bitfieldlabs/afterglow/afterglow_whitestar_pcb_v21/afterglow_whitestar_pcb_20_render.jpg

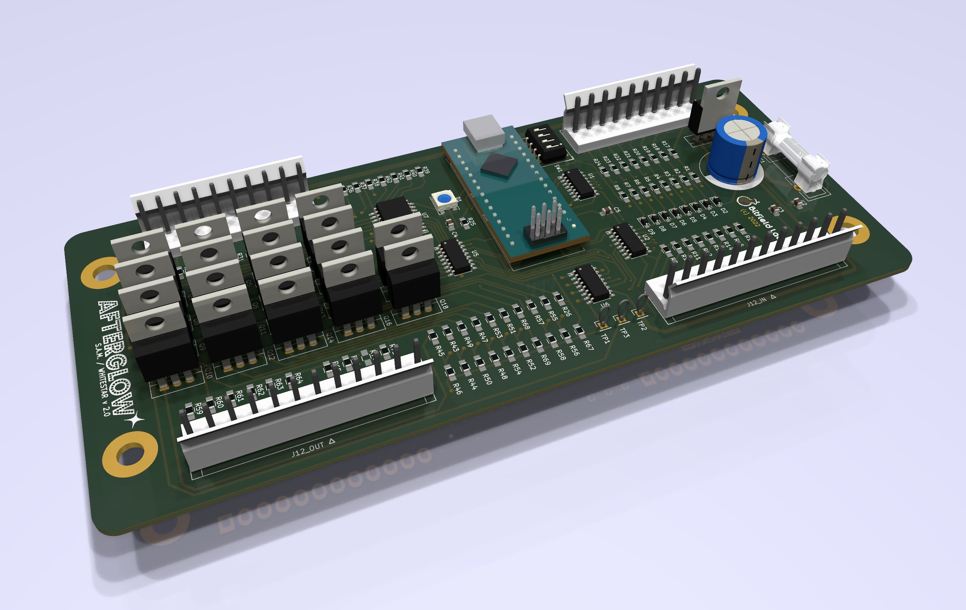
afterglow_whitestar_pcb_v21/afterglow_whitestar_pcb_20_render.jpg
