bitfieldlabs/afterglow/artwork/afterglow_config_v01.png

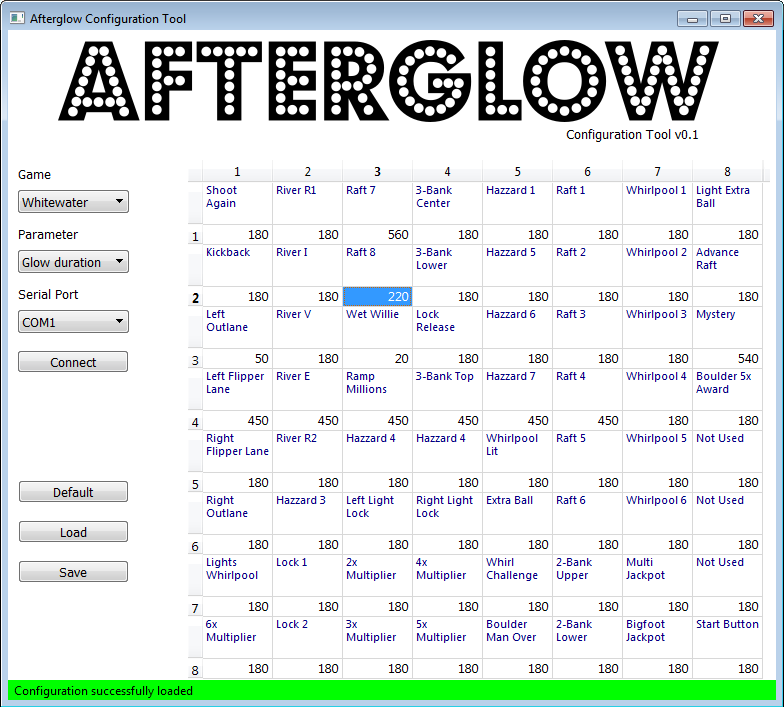
artwork/afterglow_config_v01.png
