bitfieldlabs/afterglow/docu/images/afterglow_config_0.7.png

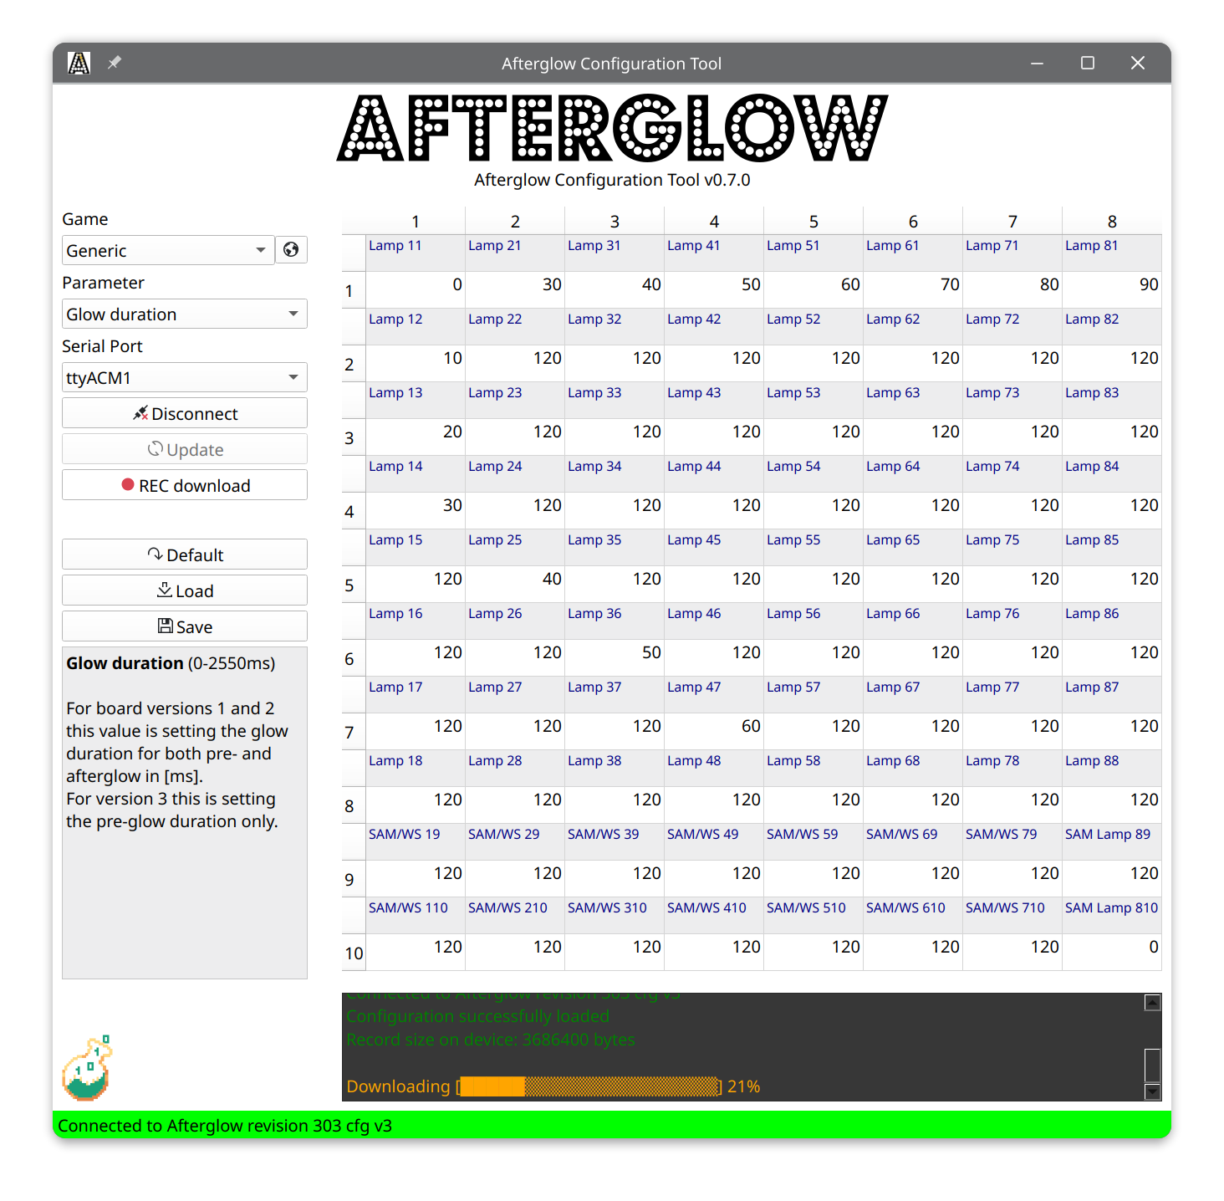
docu/images/afterglow_config_0.7.png
