bitfieldlabs/afterglow/docu/images/ag_30_dip.jpg

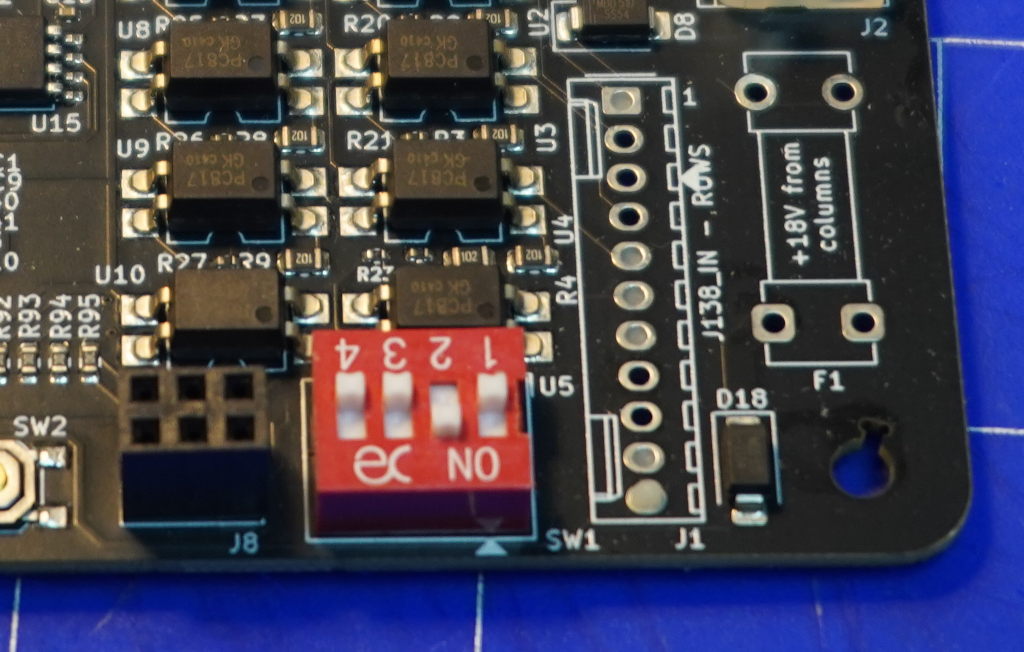
docu/images/ag_30_dip.jpg
