bitfieldlabs/afterglow/docu/images/ag_30_hats.jpg

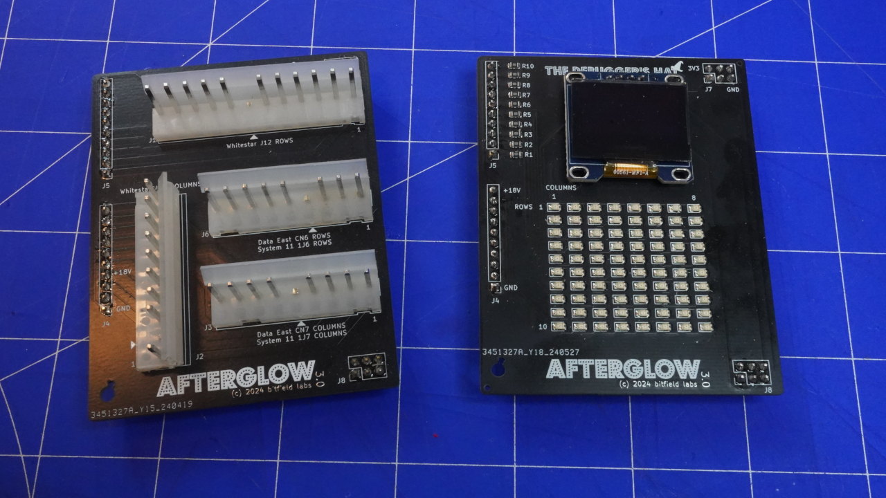
docu/images/ag_30_hats.jpg
