bitfieldlabs/afterglow/docu/images/ag_30g.jpg

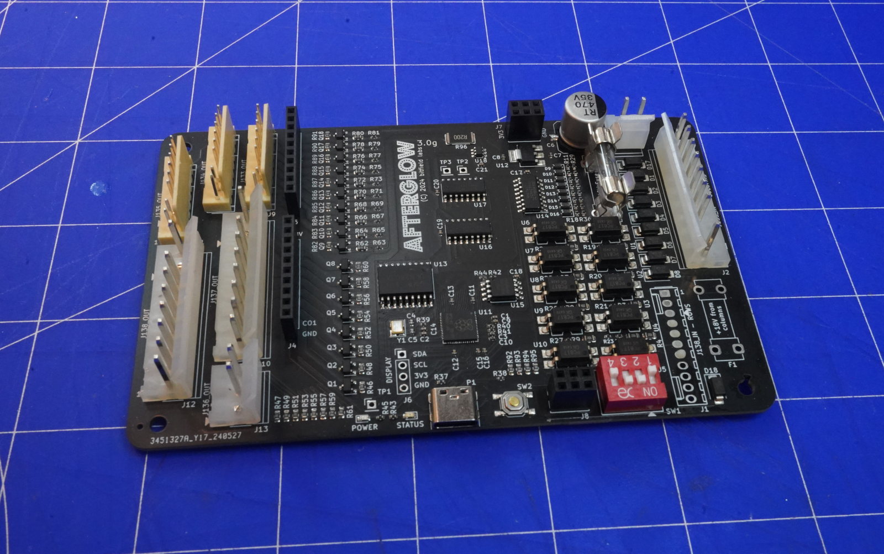
docu/images/ag_30g.jpg
