bitfieldlabs/afterglow/docu/images/ag_v13_mounting.jpg

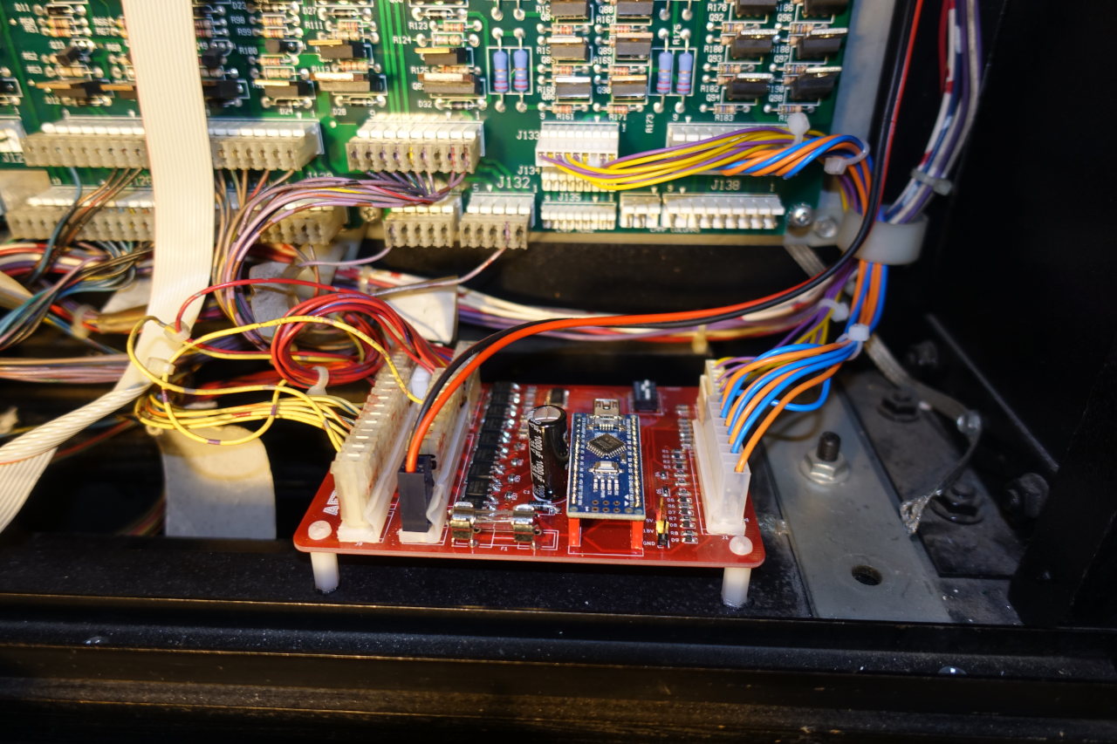
docu/images/ag_v13_mounting.jpg
