bitfieldlabs/afterglow/docu/images/ag_v13_mounting_2.jpg

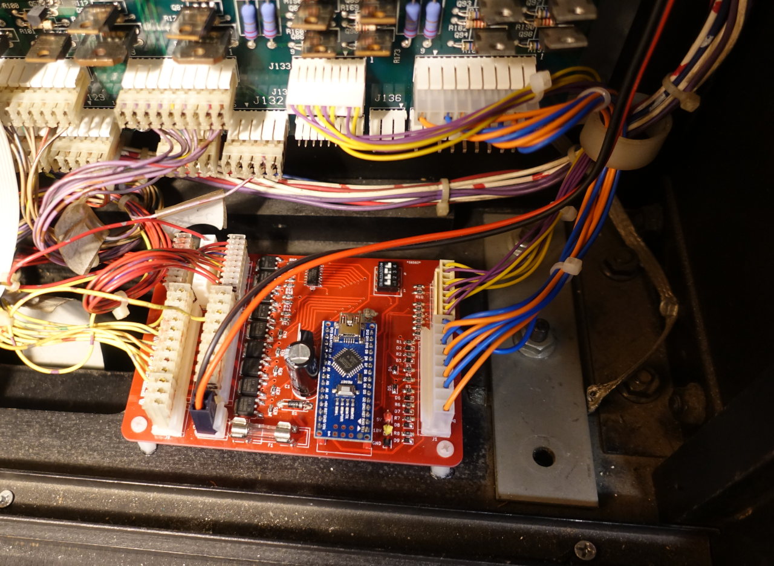
docu/images/ag_v13_mounting_2.jpg
