bitfieldlabs/afterglow/docu/images/ag_v13_mounting_3.jpg

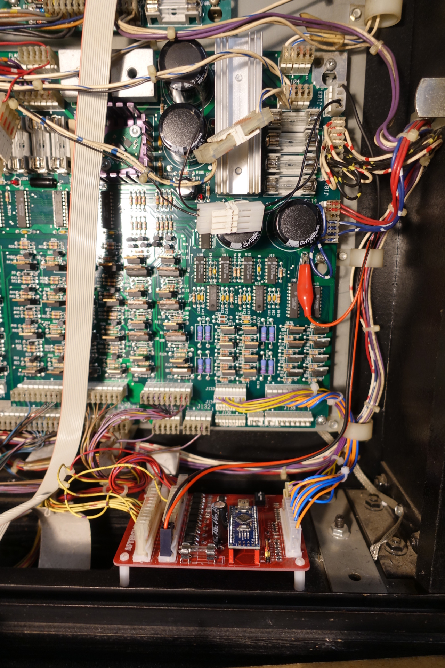
docu/images/ag_v13_mounting_3.jpg
