bitfieldlabs/afterglow/docu/images/ag_whitestar_mounting.jpg

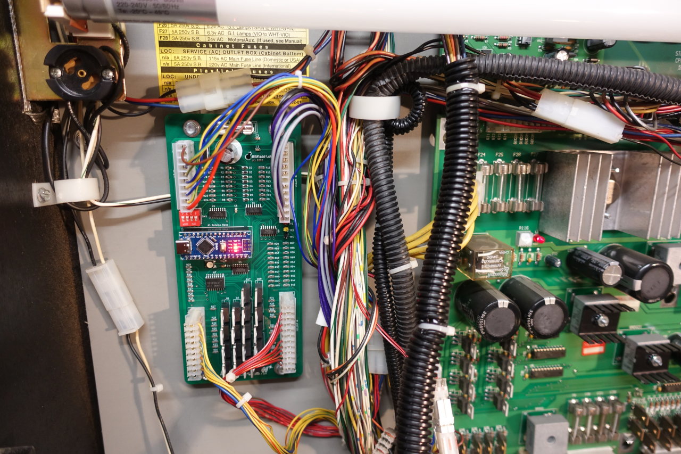
docu/images/ag_whitestar_mounting.jpg
