bitfieldlabs/afterglow/docu/images/china_led.jpg

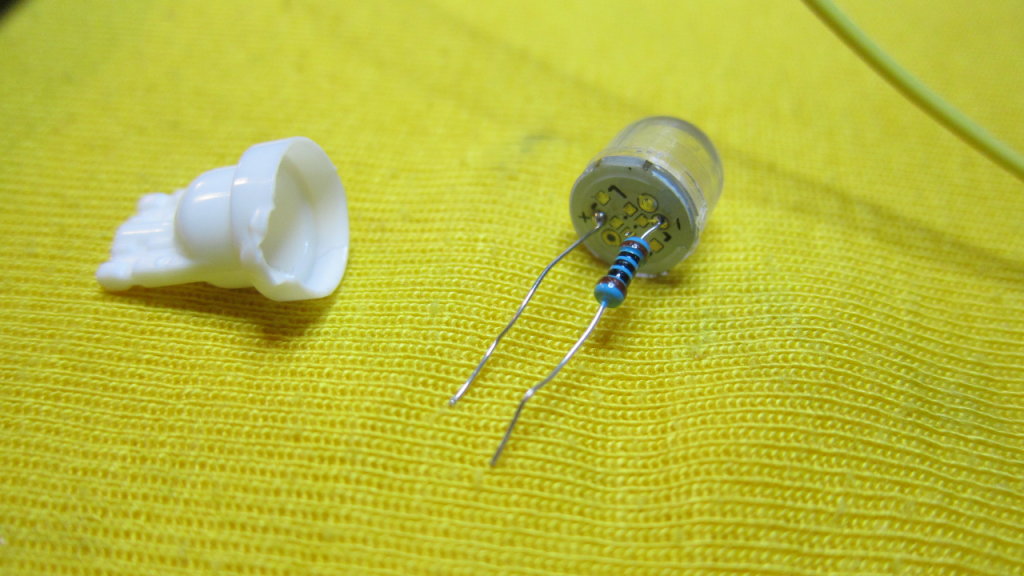
docu/images/china_led.jpg
