bitfieldlabs/afterglow/docu/images/config_switch.jpg

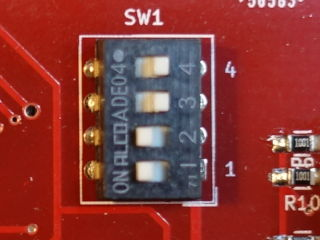
docu/images/config_switch.jpg
