bitfieldlabs/afterglow/docu/images/pcb_v10_inc.jpg

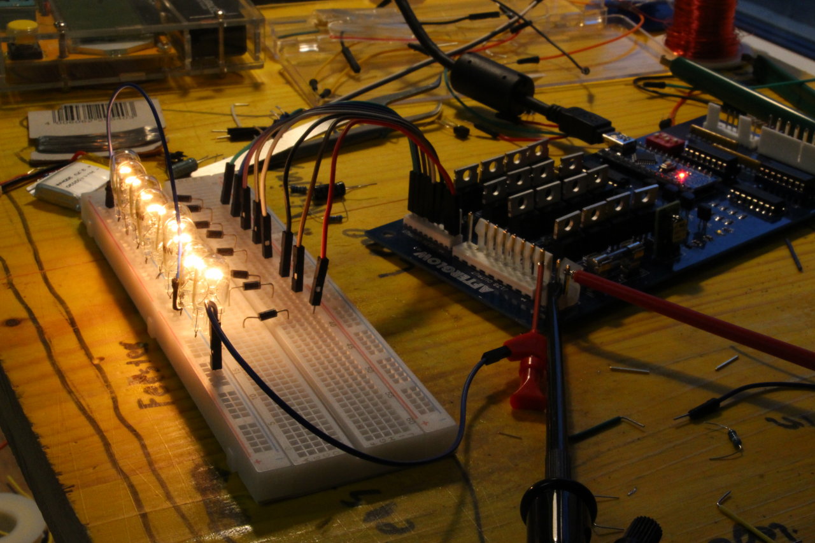
docu/images/pcb_v10_inc.jpg
