bitfieldlabs/afterglow/docu/images/pcb_v11_poulated.jpg

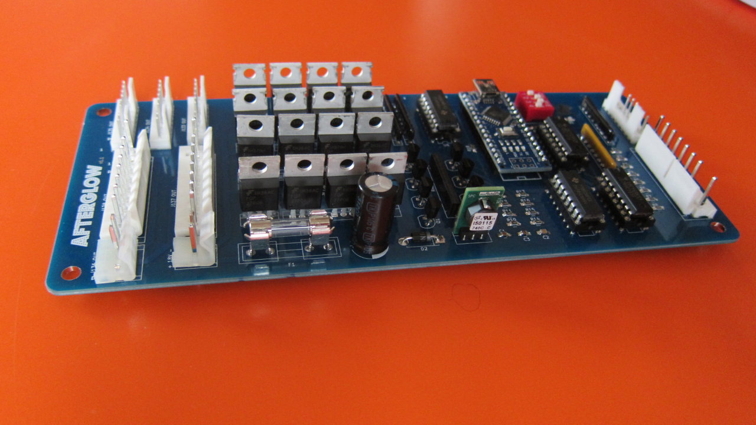
docu/images/pcb_v11_poulated.jpg
