bitfieldlabs/afterglow/docu/images/pcb_v13_populated.jpg

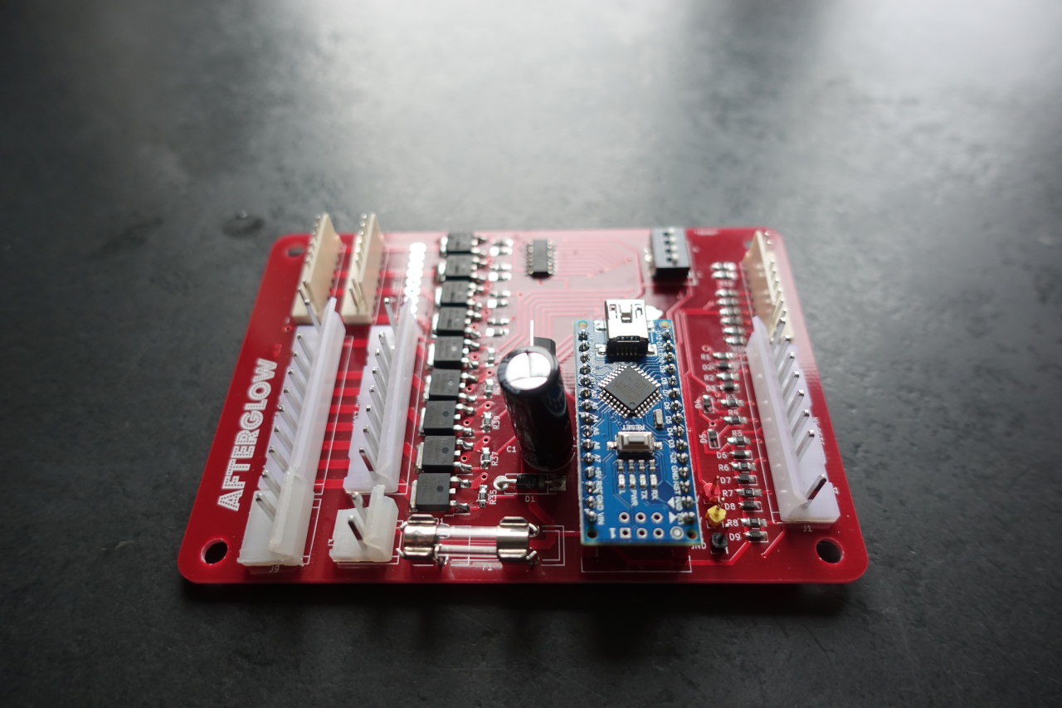
docu/images/pcb_v13_populated.jpg
