bitfieldlabs/afterglow/docu/images/pcb_v14_populated.jpg

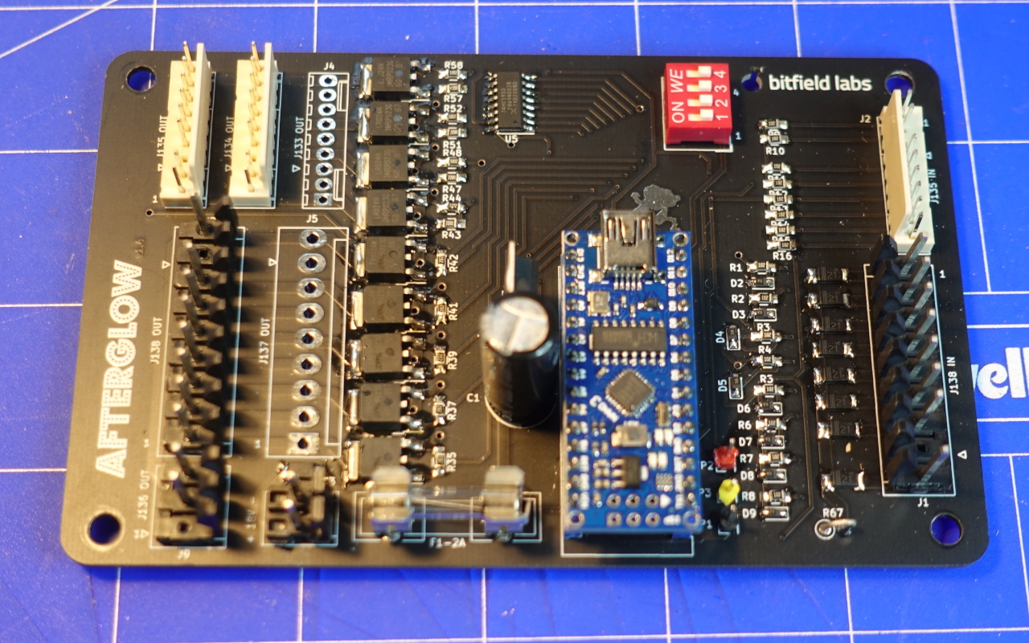
docu/images/pcb_v14_populated.jpg
