bitfieldlabs/afterglow/docu/images/pcb_v15_populated.jpg

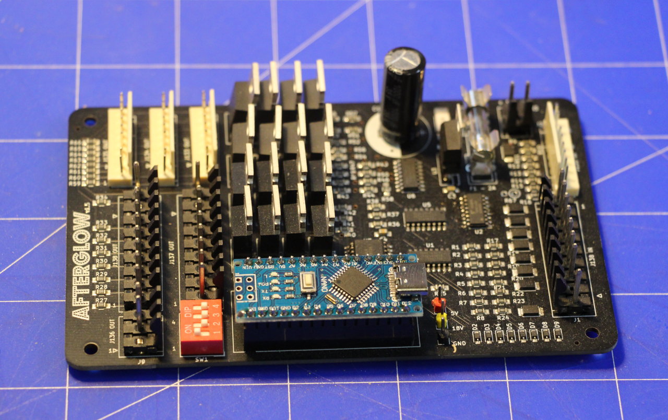
docu/images/pcb_v15_populated.jpg
