bitfieldlabs/afterglow/docu/images/pcb_v30_render.jpg

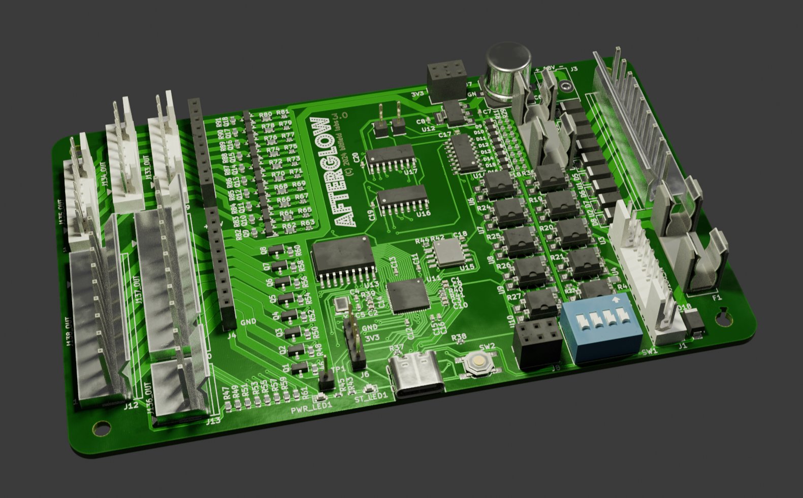
docu/images/pcb_v30_render.jpg
