bitfieldlabs/afterglow/scopes/AG/col1_col2_attract_mode.png

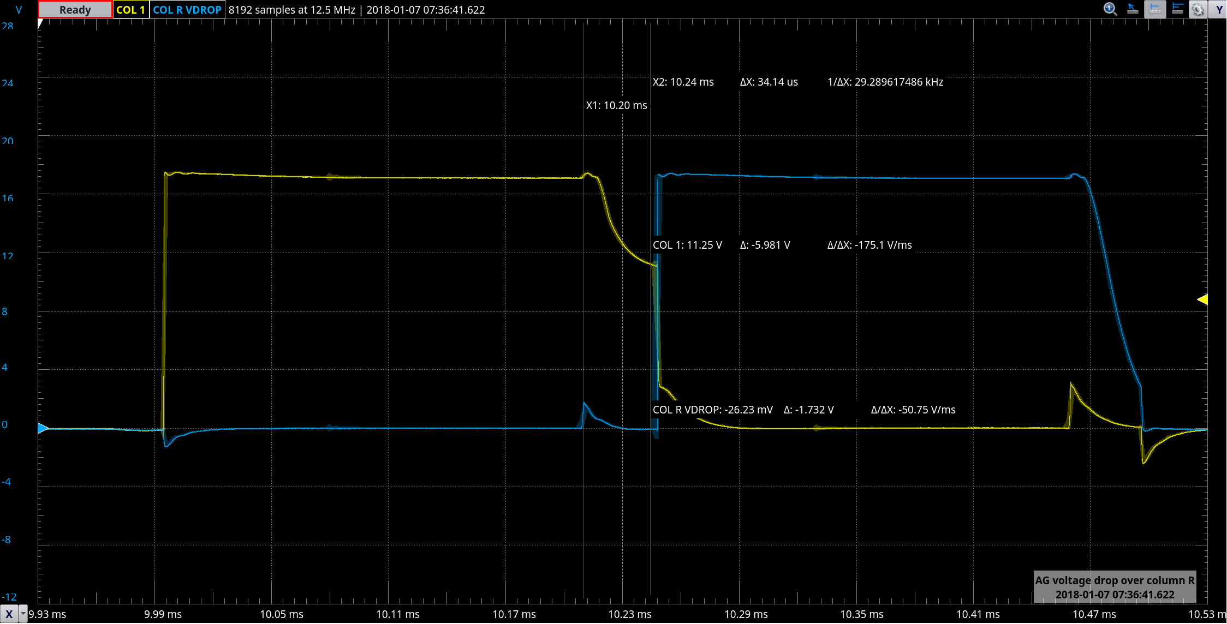
scopes/AG/col1_col2_attract_mode.png
