bitfieldlabs/afterglow/scopes/AG/vdrop_over_volumn_R.png

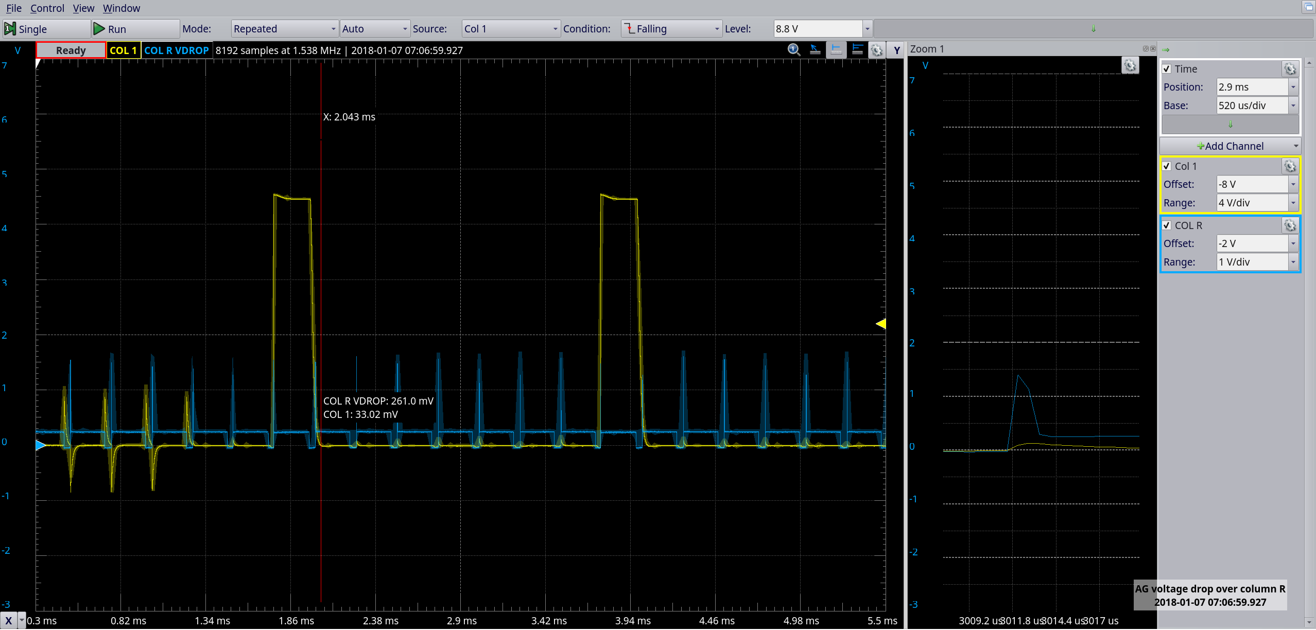
scopes/AG/vdrop_over_volumn_R.png
