bitfieldlabs/afterglow/scopes/AG/vdrop_over_volumn_R_col1_on_zoom.png

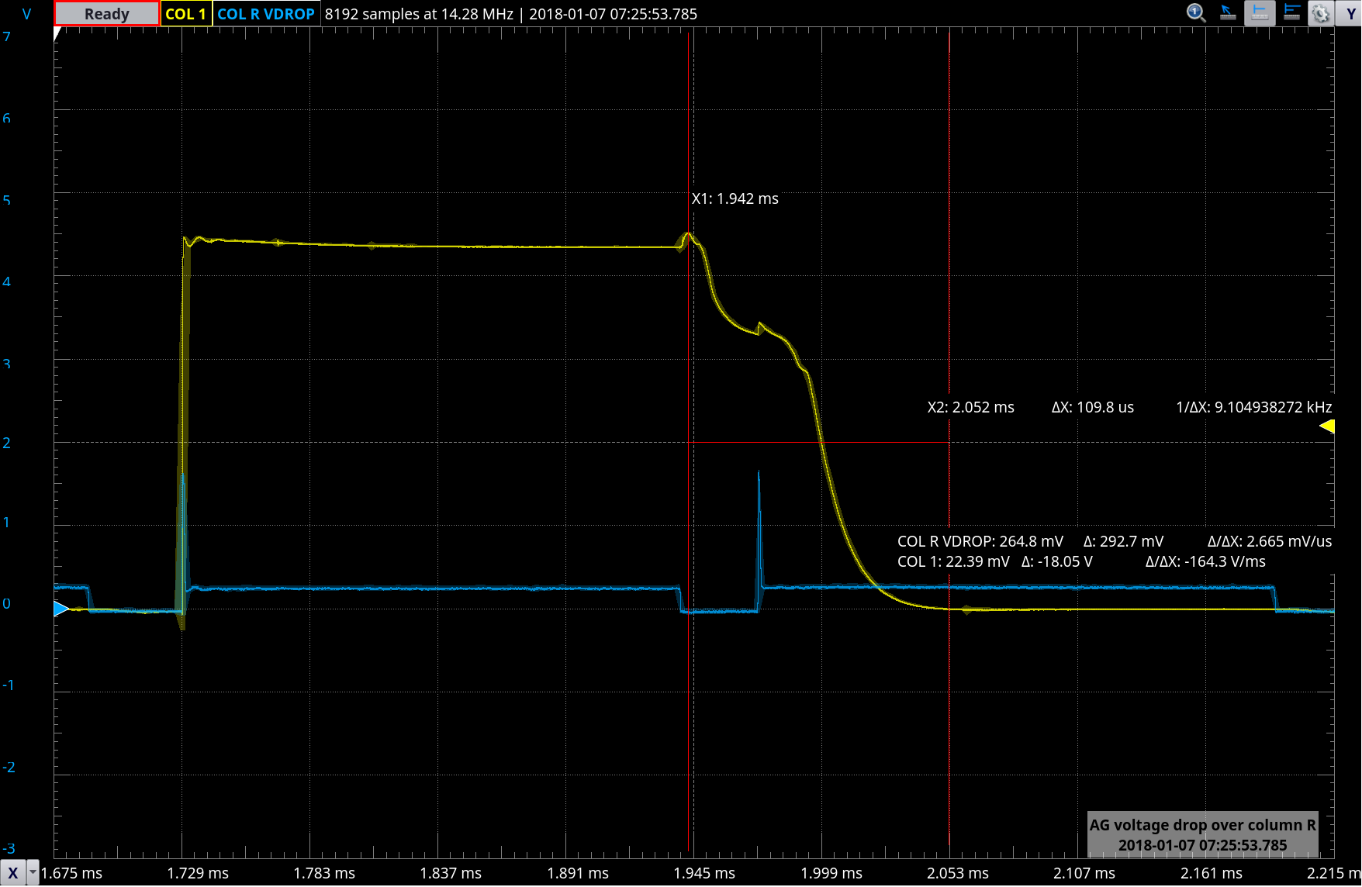
scopes/AG/vdrop_over_volumn_R_col1_on_zoom.png
