bitfieldlabs/afterglow/scopes/AG/vdrop_over_volumn_R_lamps_off.png

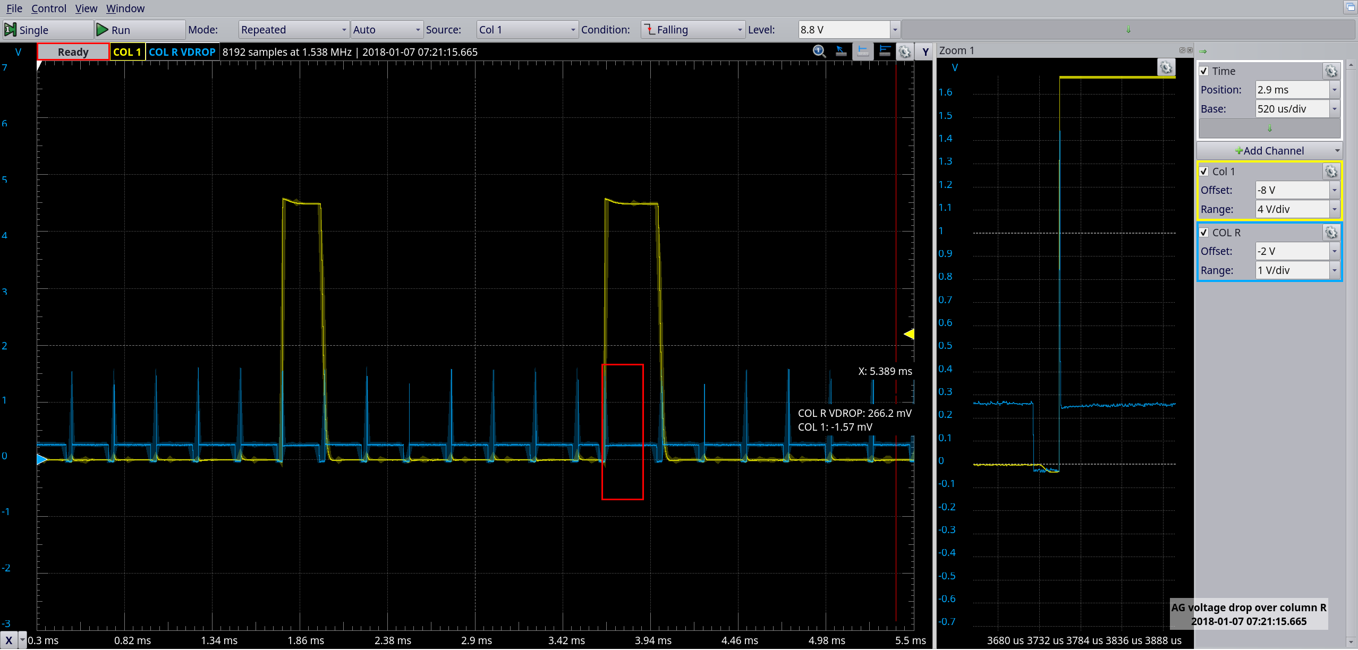
scopes/AG/vdrop_over_volumn_R_lamps_off.png
