bitfieldlabs/afterglow/scopes/AG/vdrop_over_volumn_R_lamps_off_2_annotated.png

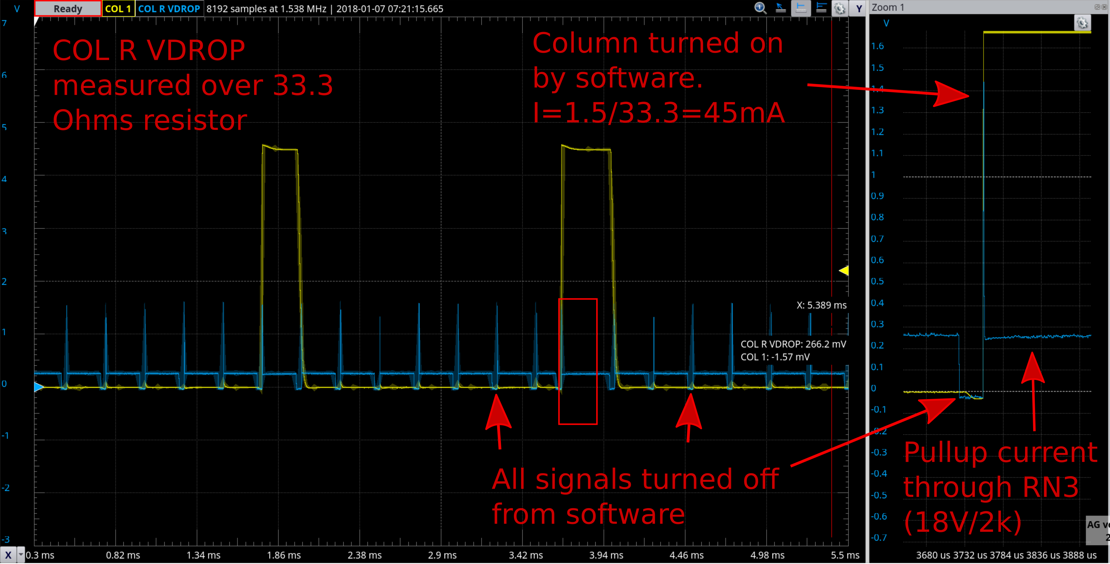
scopes/AG/vdrop_over_volumn_R_lamps_off_2_annotated.png
