bitfieldlabs/afterglow/scopes/AG/vdrop_over_volumn_R_lamps_on.png

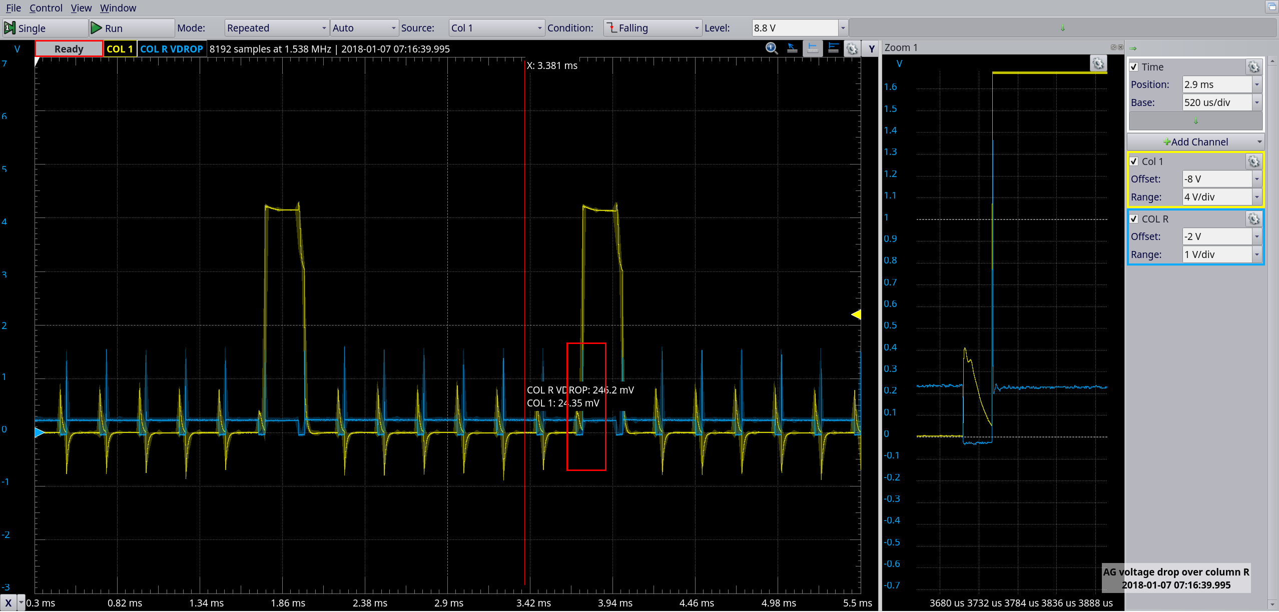
scopes/AG/vdrop_over_volumn_R_lamps_on.png
