bitfieldlabs/afterglow/scopes/AG/wh20_col1_comparison.png

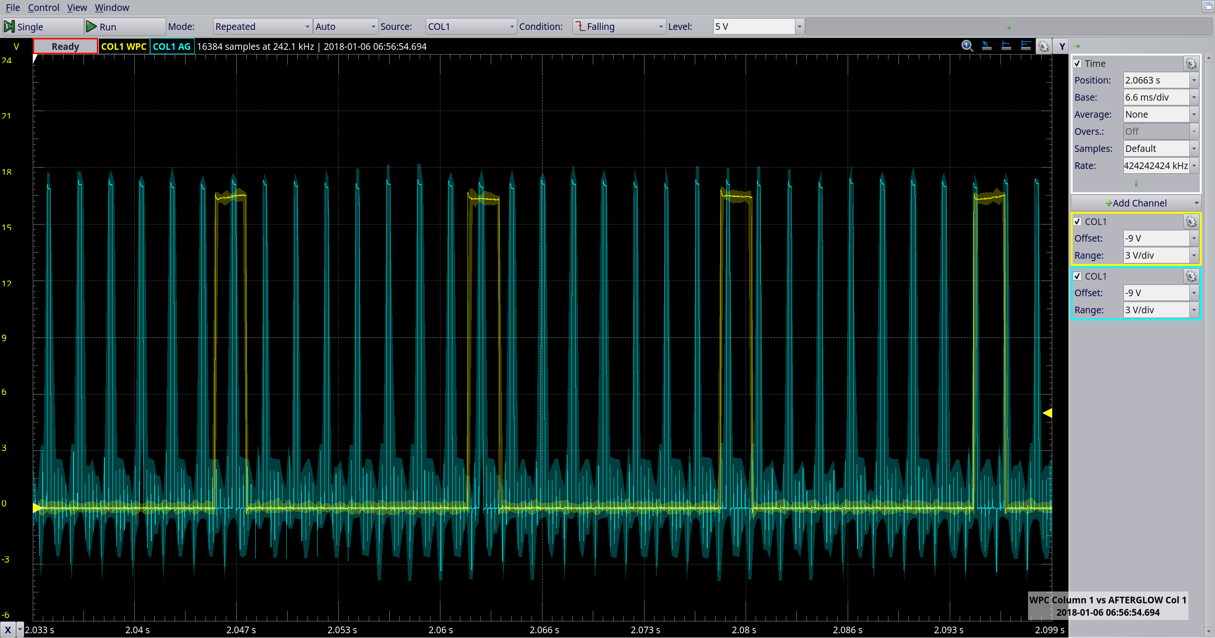
scopes/AG/wh20_col1_comparison.png
