bitfieldlabs/afterglow/scopes/AG/wh20_col1_noise.png

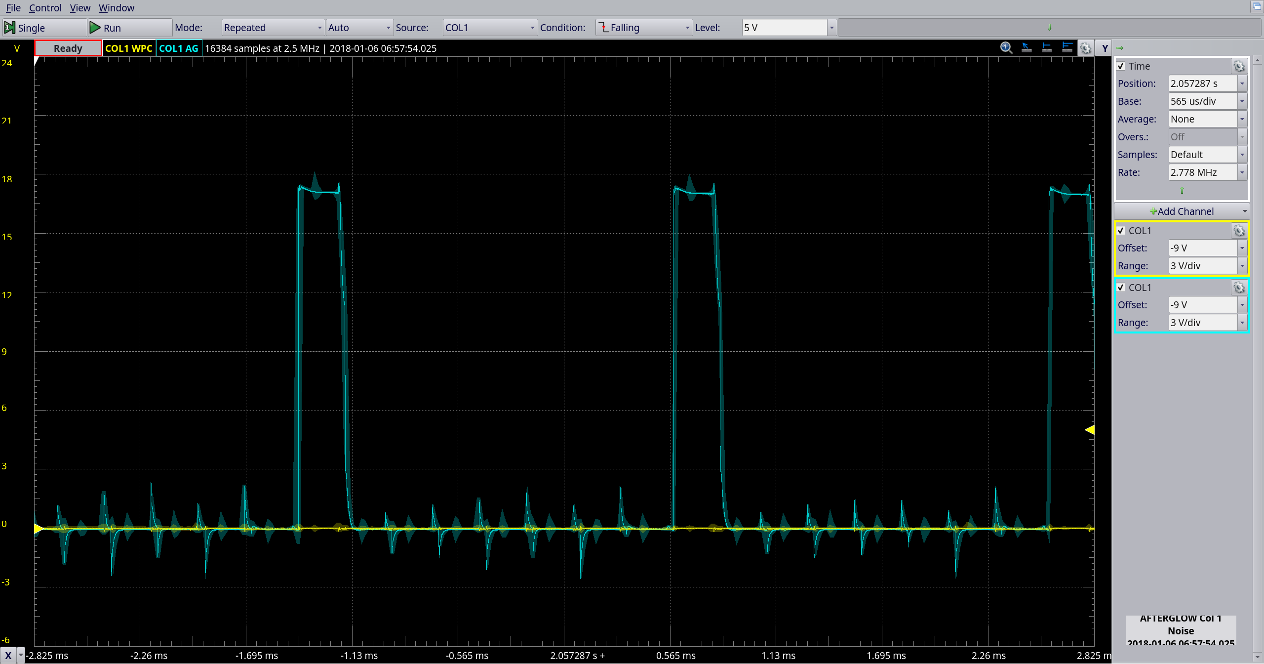
scopes/AG/wh20_col1_noise.png
