bitfieldlabs/afterglow/scopes/AG_SMD/col1_col2_lamps_connected.png

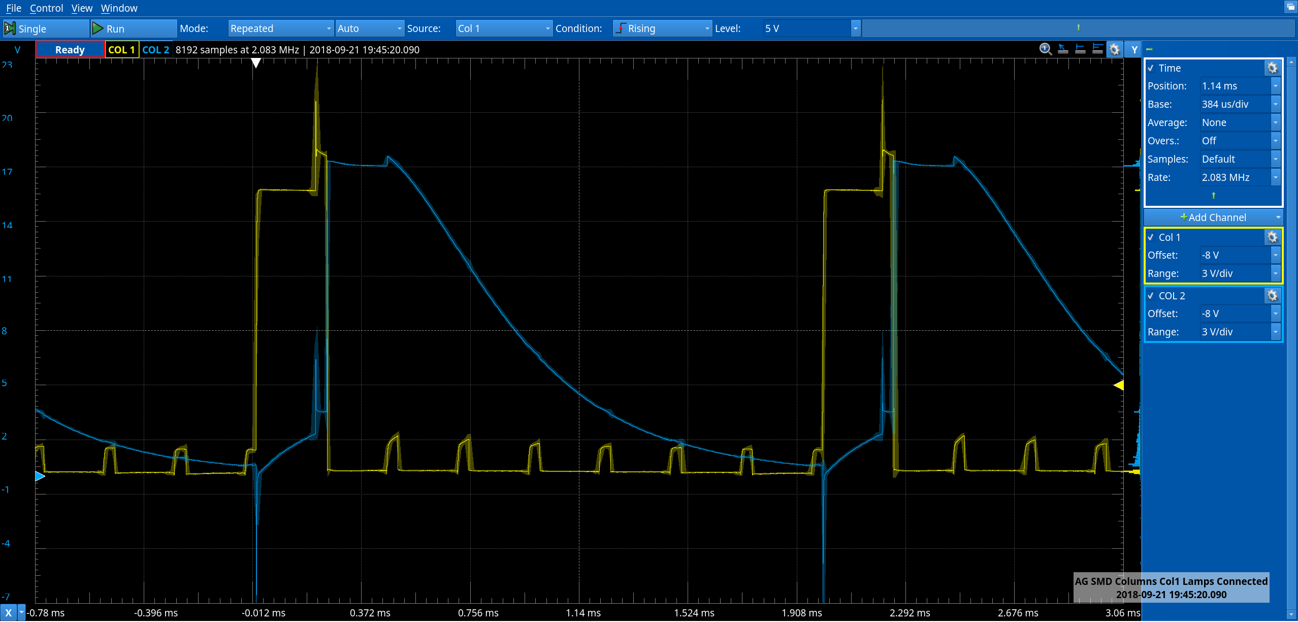
scopes/AG_SMD/col1_col2_lamps_connected.png
