bitfieldlabs/afterglow/scopes/AG_SMD/col1_col2_no_lamps_connected.png

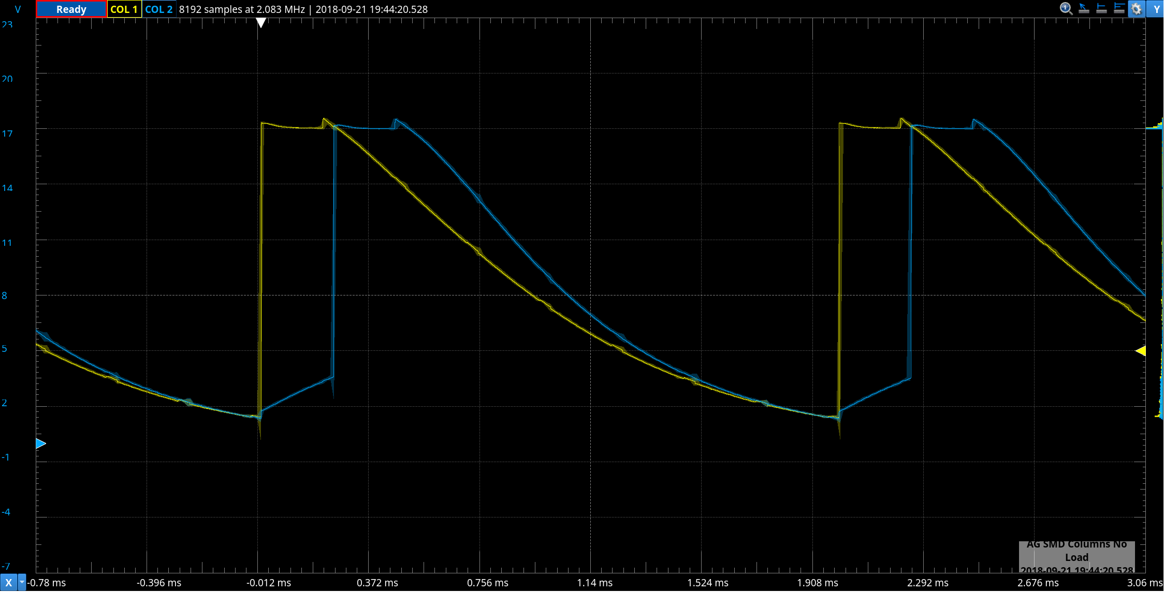
scopes/AG_SMD/col1_col2_no_lamps_connected.png
