bitfieldlabs/afterglow/scopes/AG_SMD/col1_row1_lamp_on.png

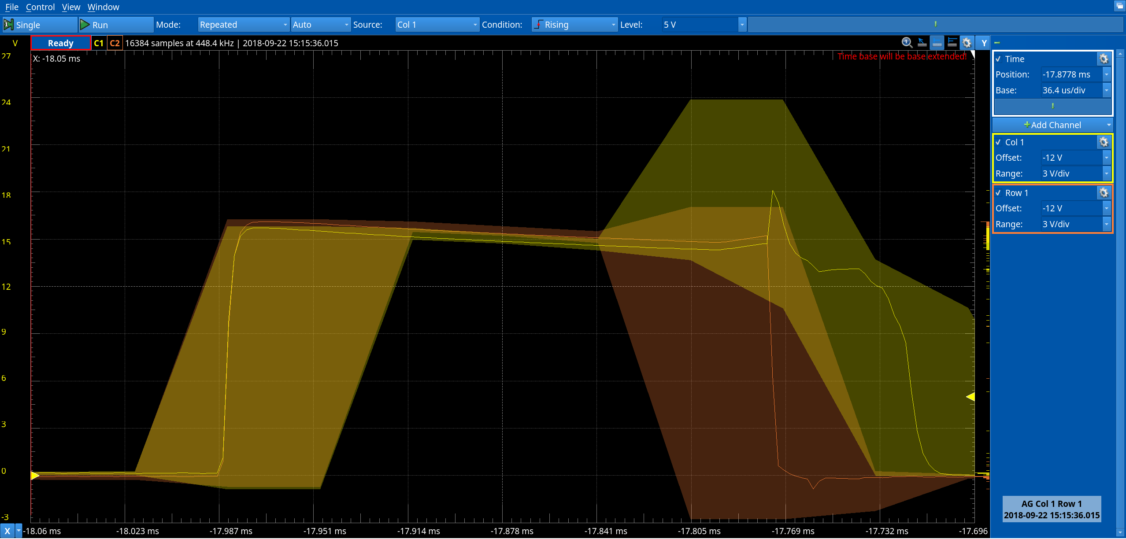
scopes/AG_SMD/col1_row1_lamp_on.png
