bitfieldlabs/afterglow/scopes/AG_SMD/col1_row1_vdrop_r27.png

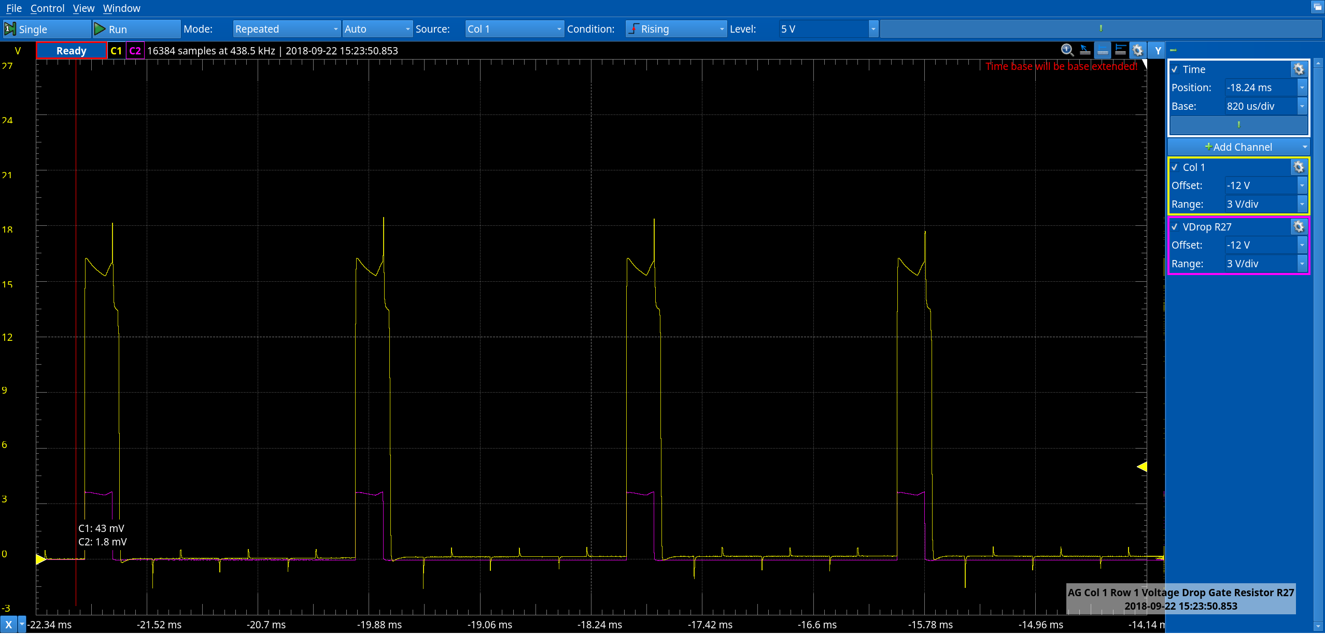
scopes/AG_SMD/col1_row1_vdrop_r27.png
