bitfieldlabs/afterglow/scopes/AG_SMD/creature_voltage_stop.png

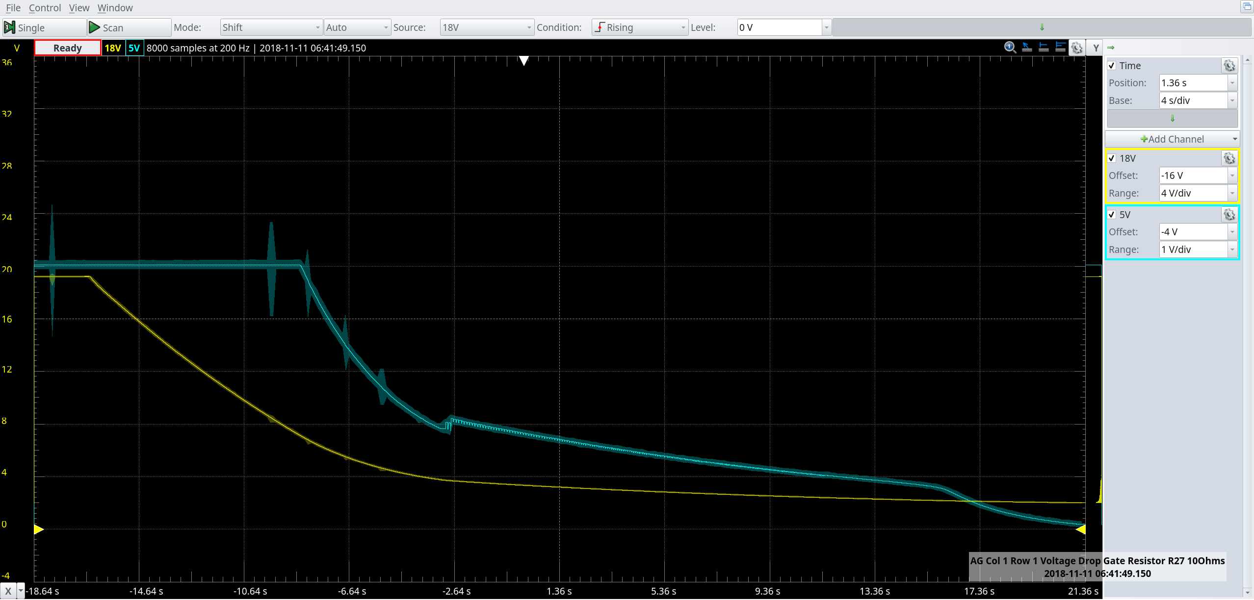
scopes/AG_SMD/creature_voltage_stop.png
