bitfieldlabs/afterglow/scopes/data_east_columns.png

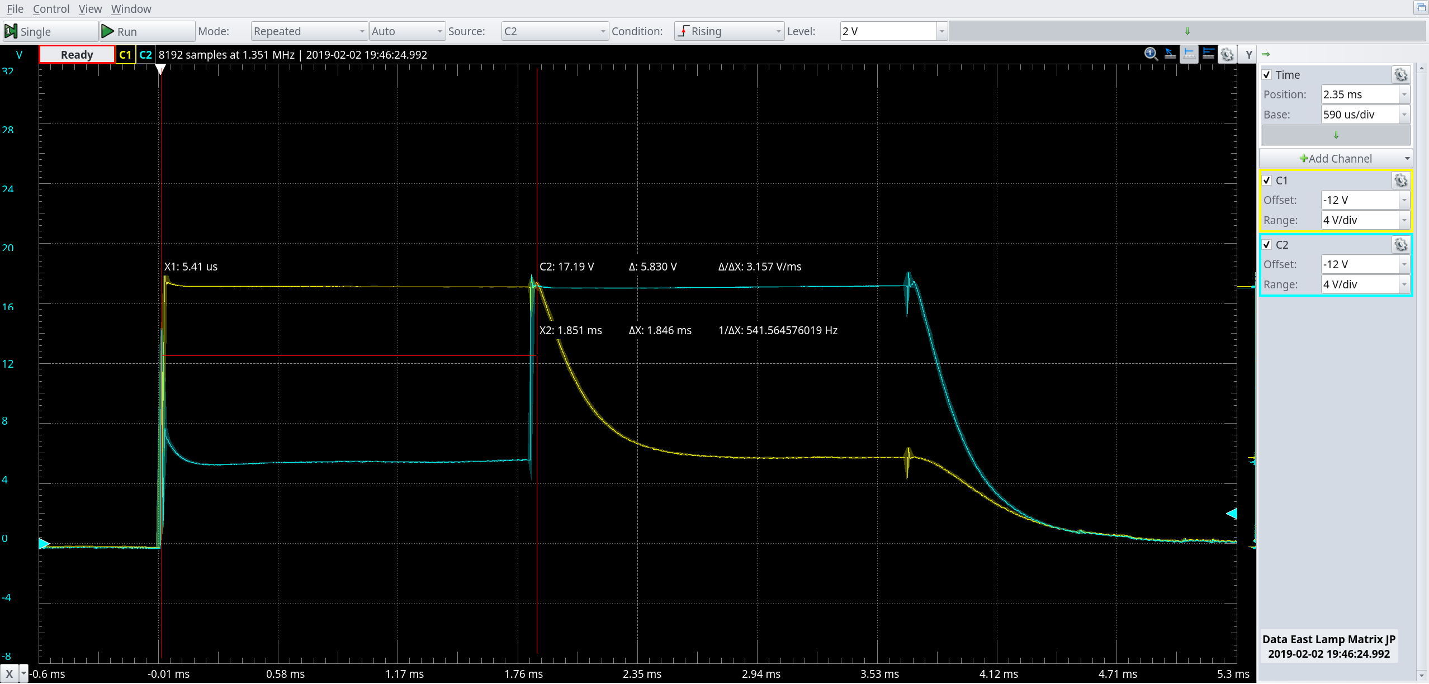
scopes/data_east_columns.png
