bitfieldlabs/afterglow/scopes/data_east_columns_2.png

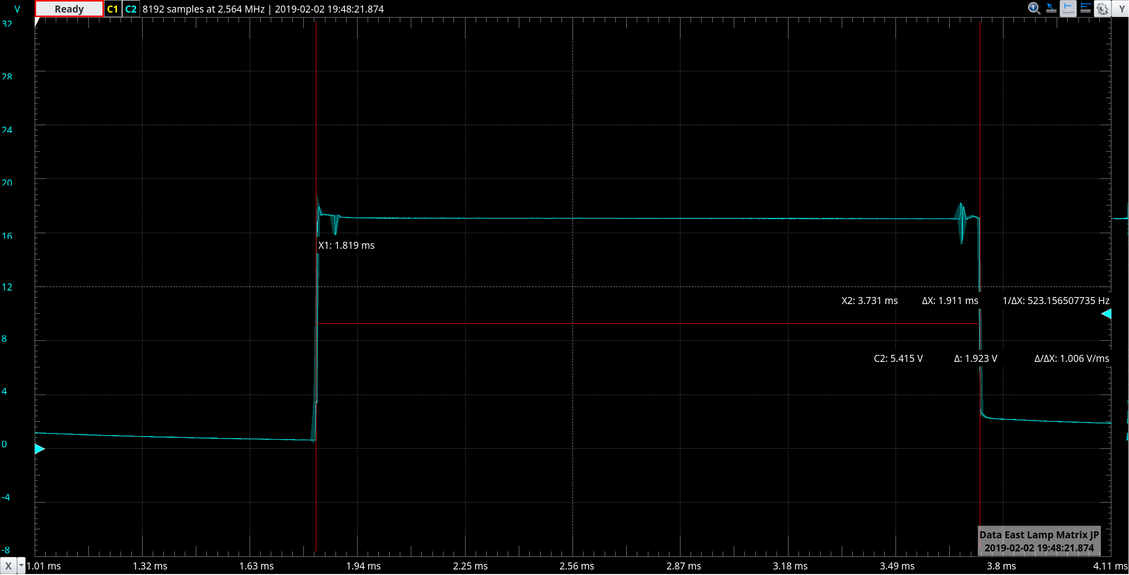
scopes/data_east_columns_2.png
