bitfieldlabs/afterglow/scopes/data_east_columns_3.png

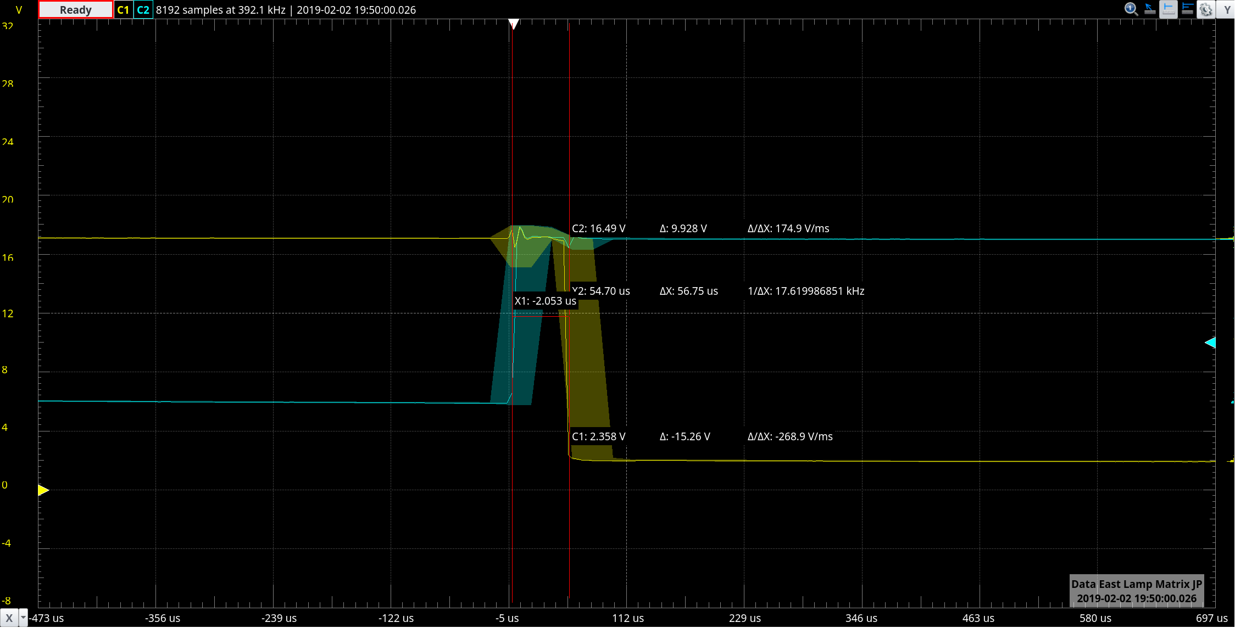
scopes/data_east_columns_3.png
