bitfieldlabs/afterglow/scopes/data_east_columns_4.png

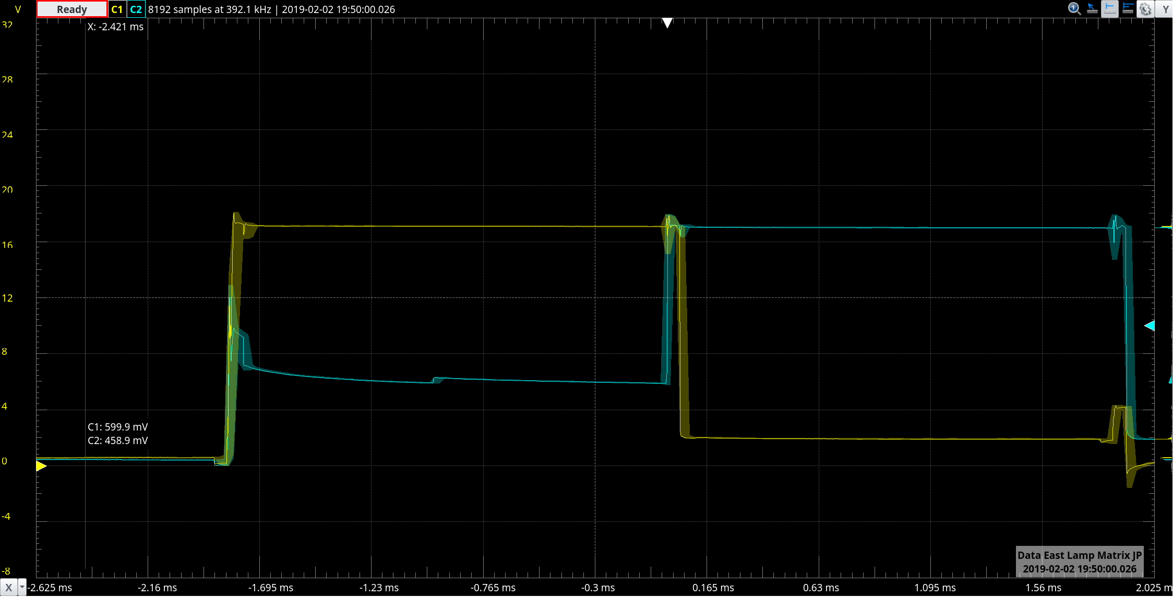
scopes/data_east_columns_4.png
