bitfieldlabs/afterglow/scopes/data_east_columns_5.png

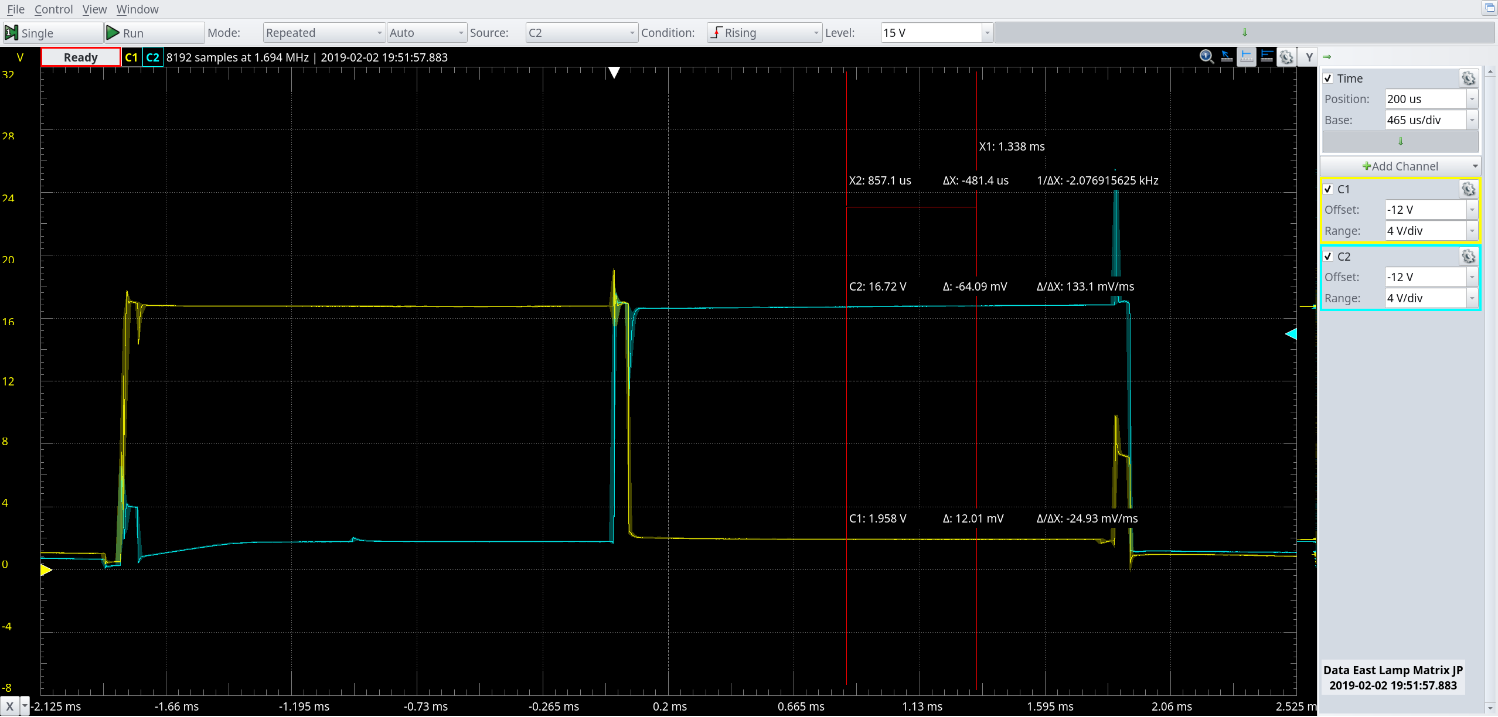
scopes/data_east_columns_5.png
