bitfieldlabs/afterglow/scopes/data_east_columns_6.png

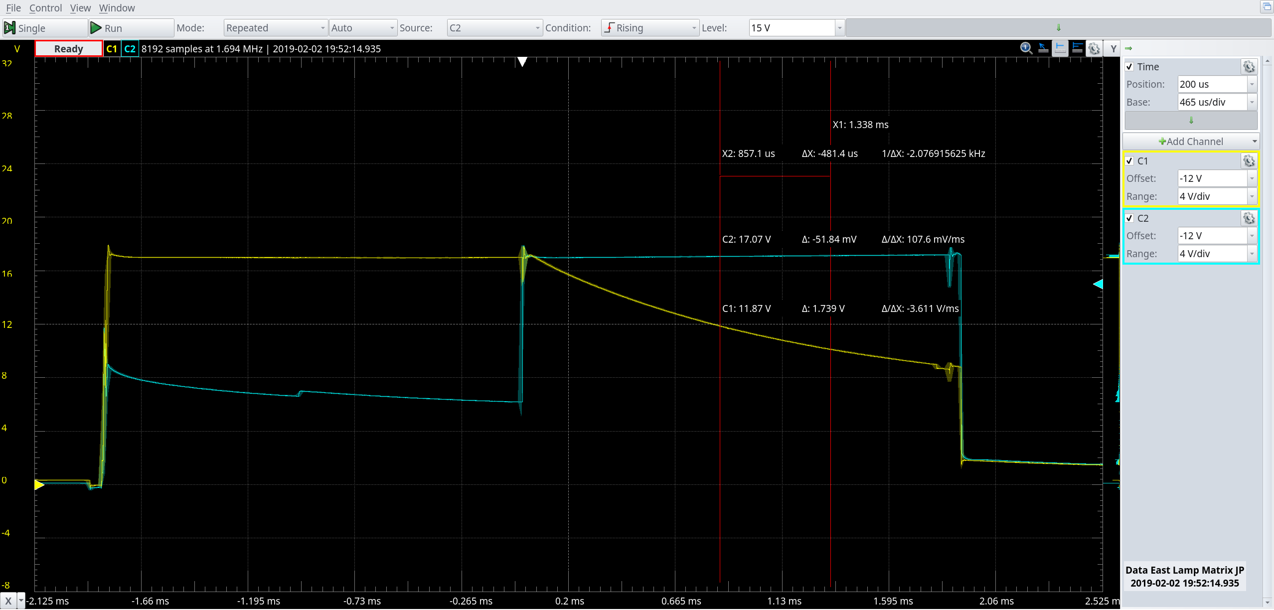
scopes/data_east_columns_6.png
