bitfieldlabs/afterglow/scopes/system_11_ww_col1_col2_2.png

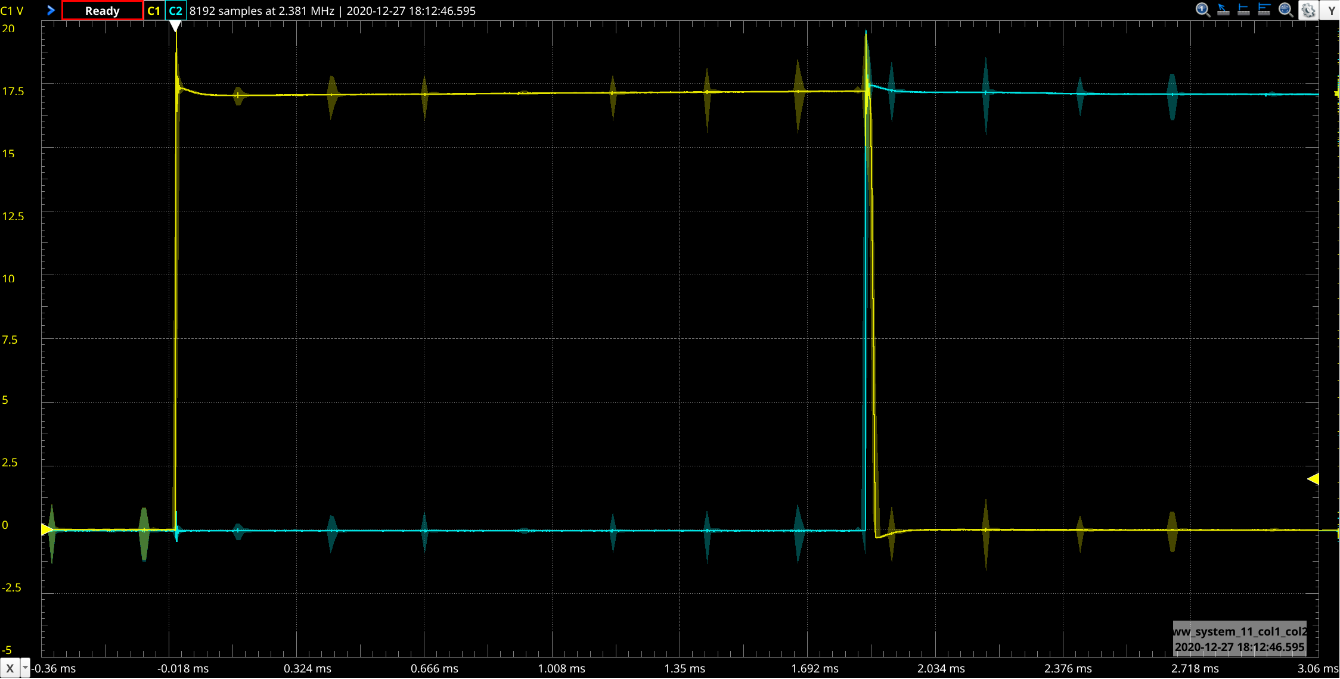
scopes/system_11_ww_col1_col2_2.png
