bitfieldlabs/afterglow/scopes/system_11_ww_col1_col2_R89_R88.png

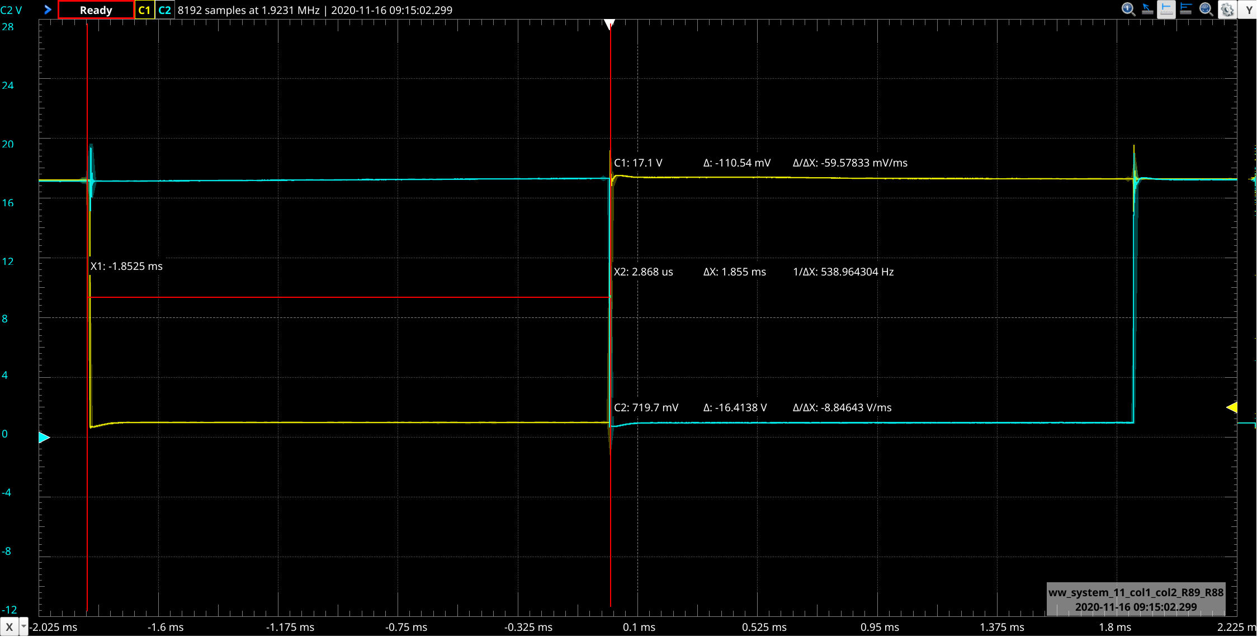
scopes/system_11_ww_col1_col2_R89_R88.png
