bitfieldlabs/afterglow/scopes/system_11_ww_col1_R89.png

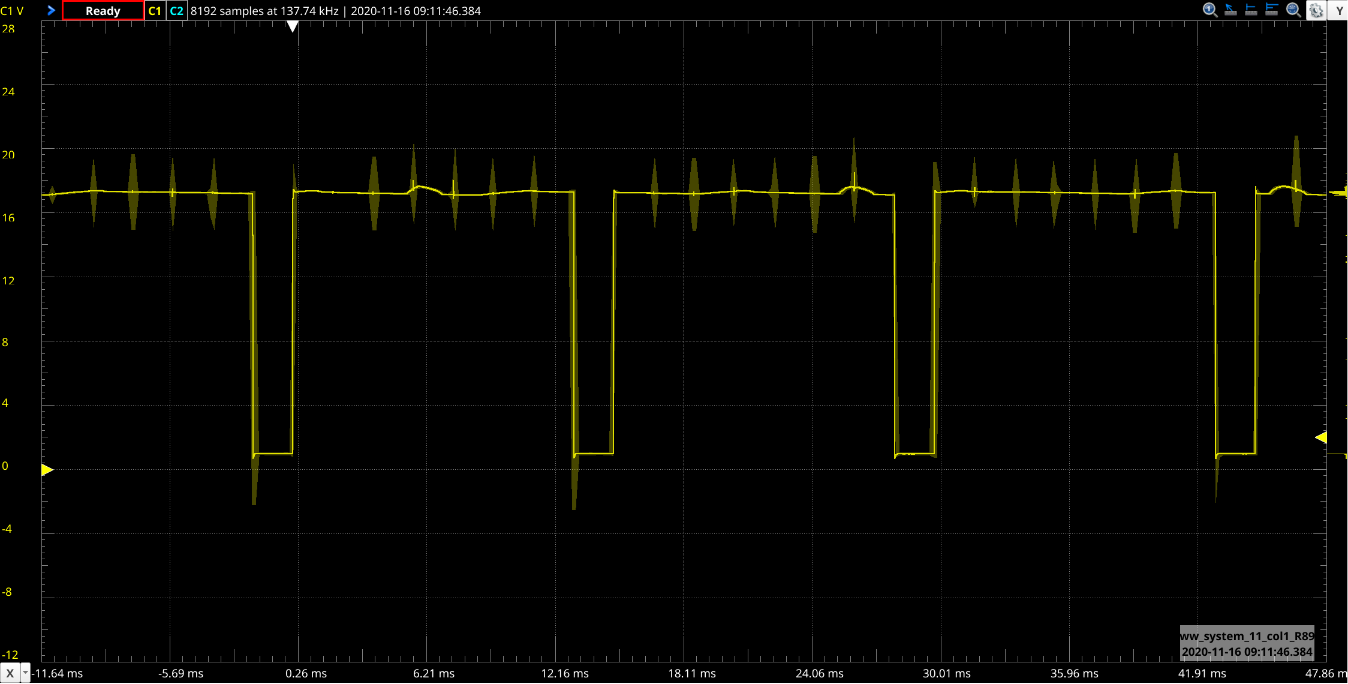
scopes/system_11_ww_col1_R89.png
