bitfieldlabs/afterglow/scopes/whitestar_ripley_C1_R1.png

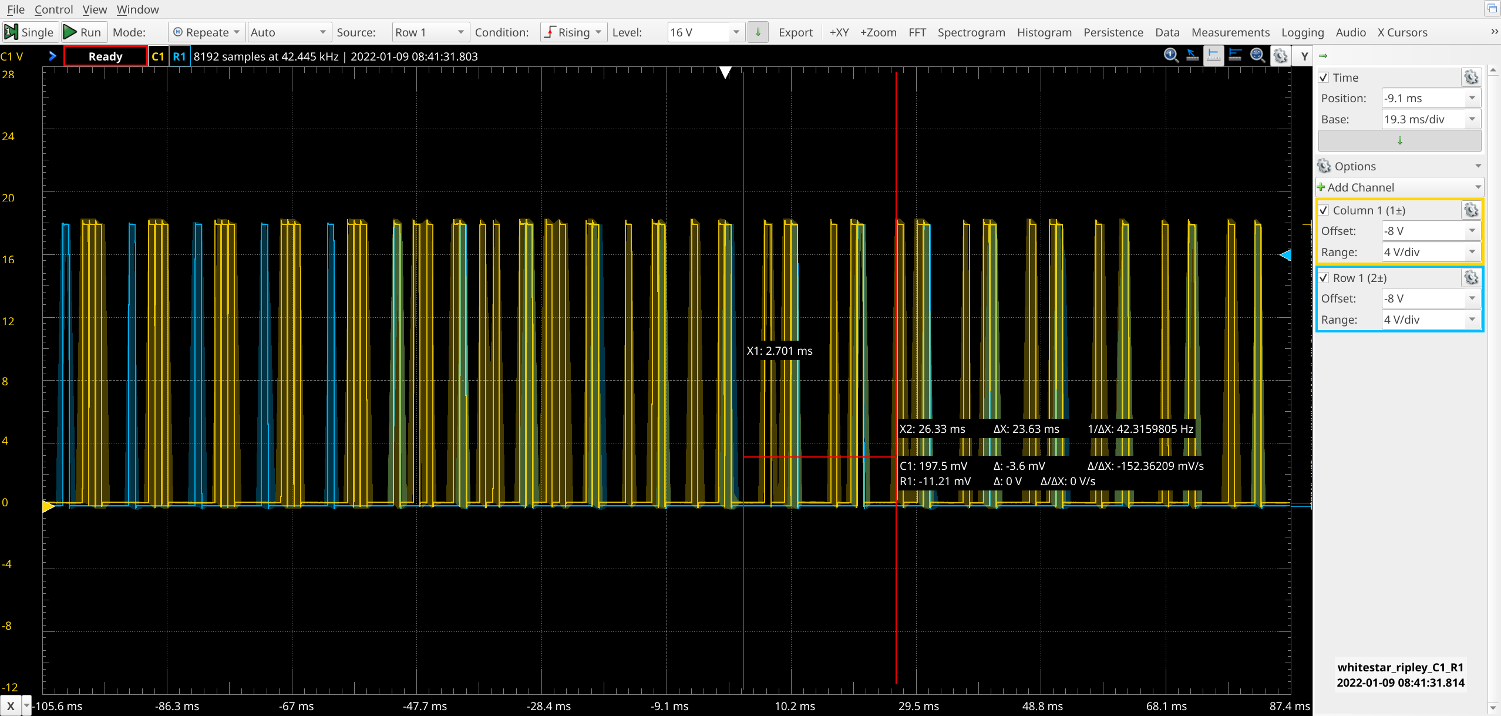
scopes/whitestar_ripley_C1_R1.png
