bitfieldlabs/afterglow/scopes/whitestar_ripley_C1_R1_closeup.png

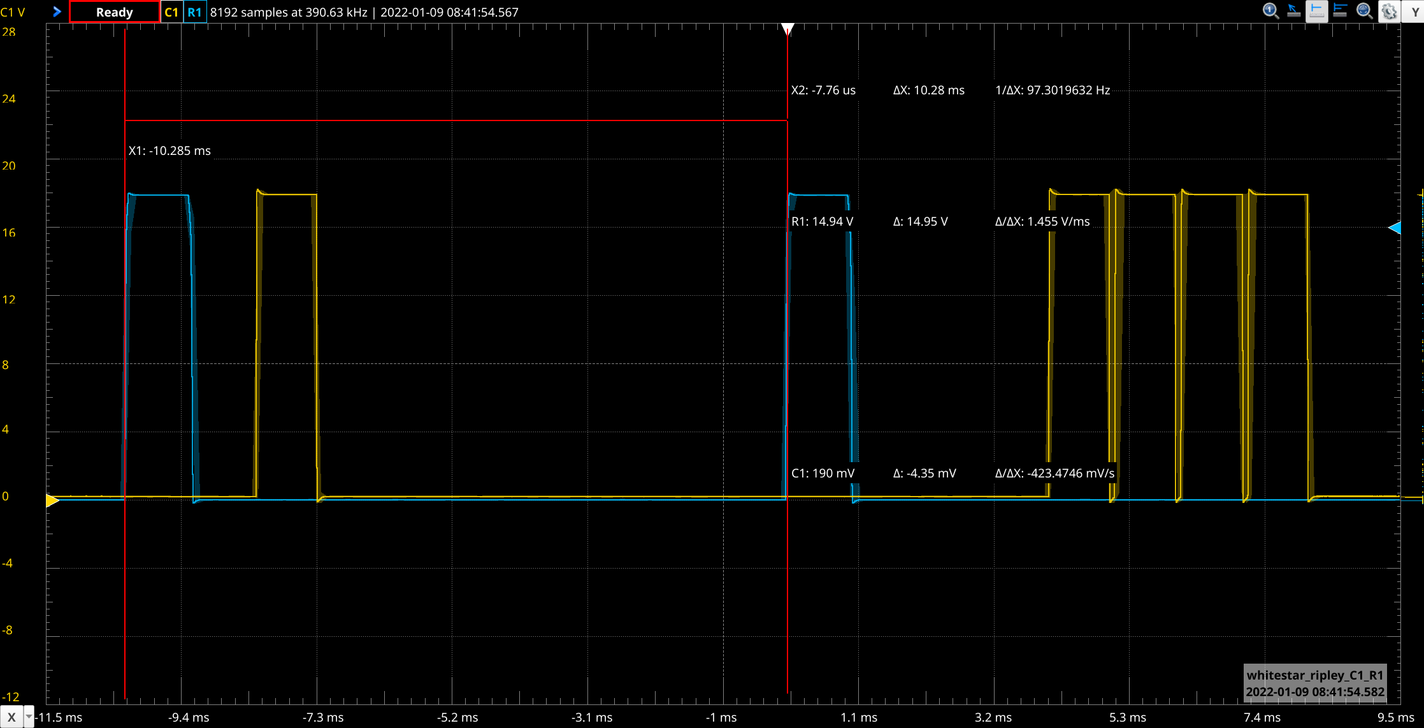
scopes/whitestar_ripley_C1_R1_closeup.png
