bitfieldlabs/afterglow/scopes/whitestar_ripley_R1_R2_closeup.png

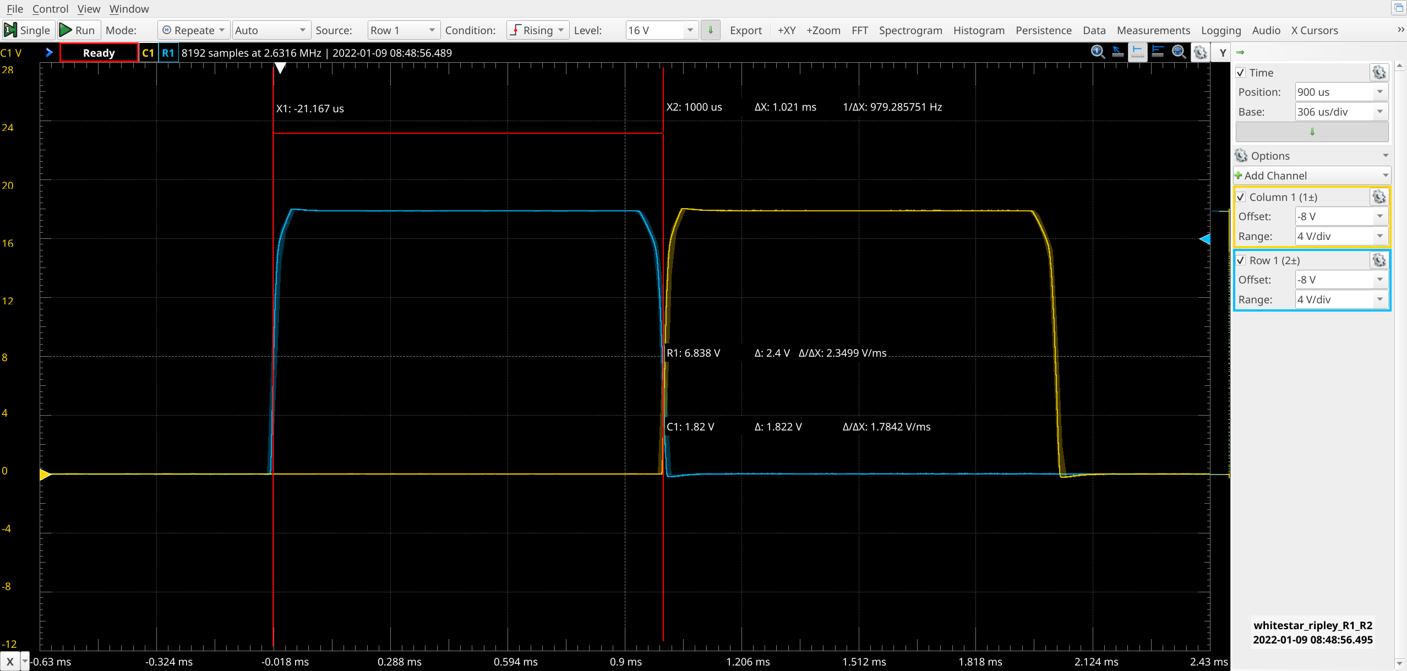
scopes/whitestar_ripley_R1_R2_closeup.png
