bitfieldlabs/afterglow/scopes/whitestar_ripley_rows_J12.png

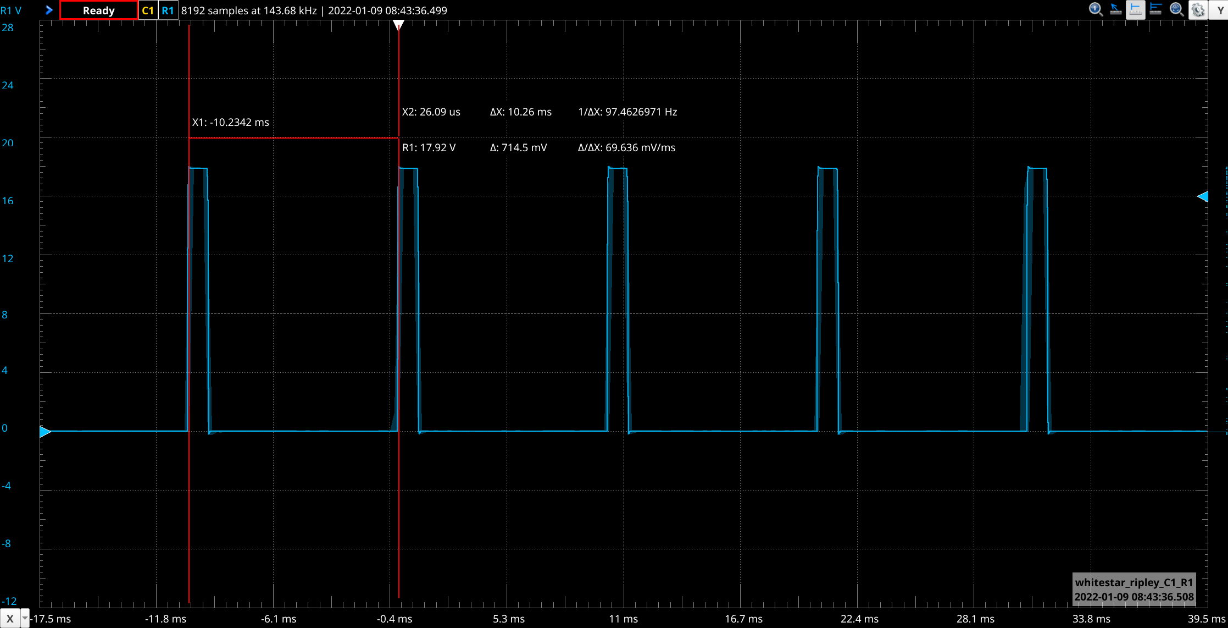
scopes/whitestar_ripley_rows_J12.png
