bitfieldlabs/afterglow/scopes/WPC/wh20_col1_col2.png

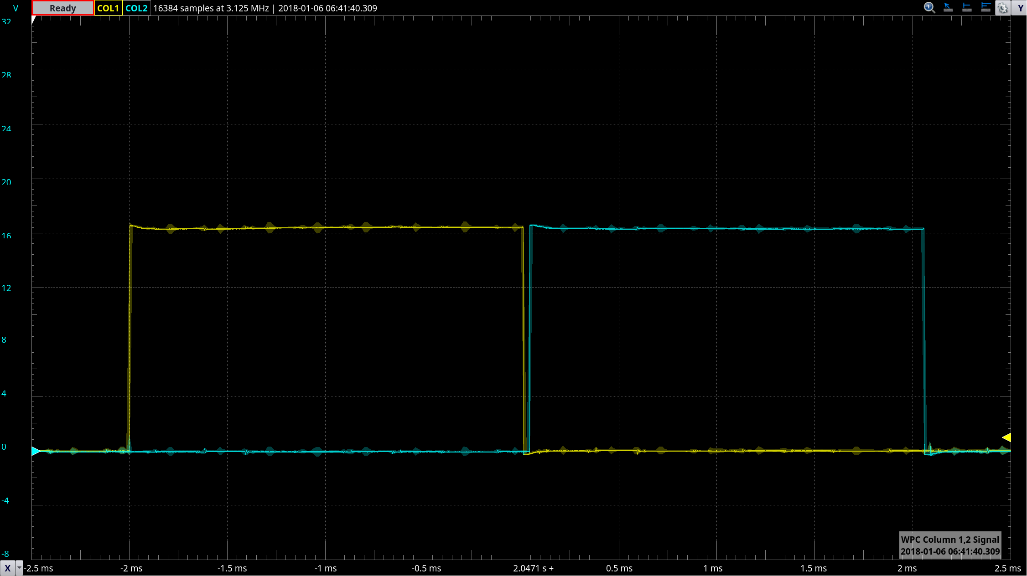
scopes/WPC/wh20_col1_col2.png
