bitfieldlabs/afterglow/scopes/WPC/wh20_col1_col2_switch_zoom.png

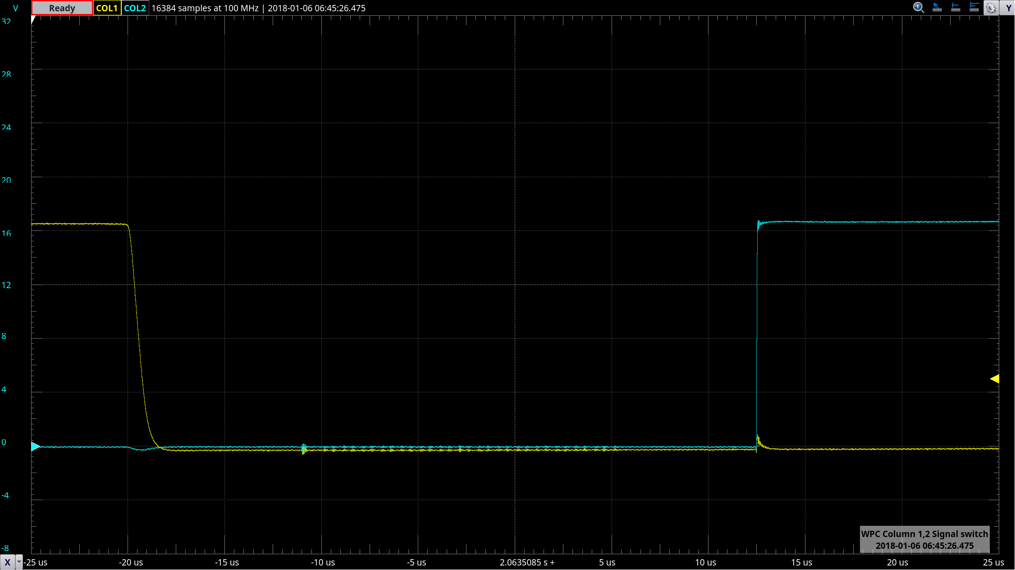
scopes/WPC/wh20_col1_col2_switch_zoom.png
