bitfieldlabs/afterglow/scopes/WPC/wh20_col1_row1.png

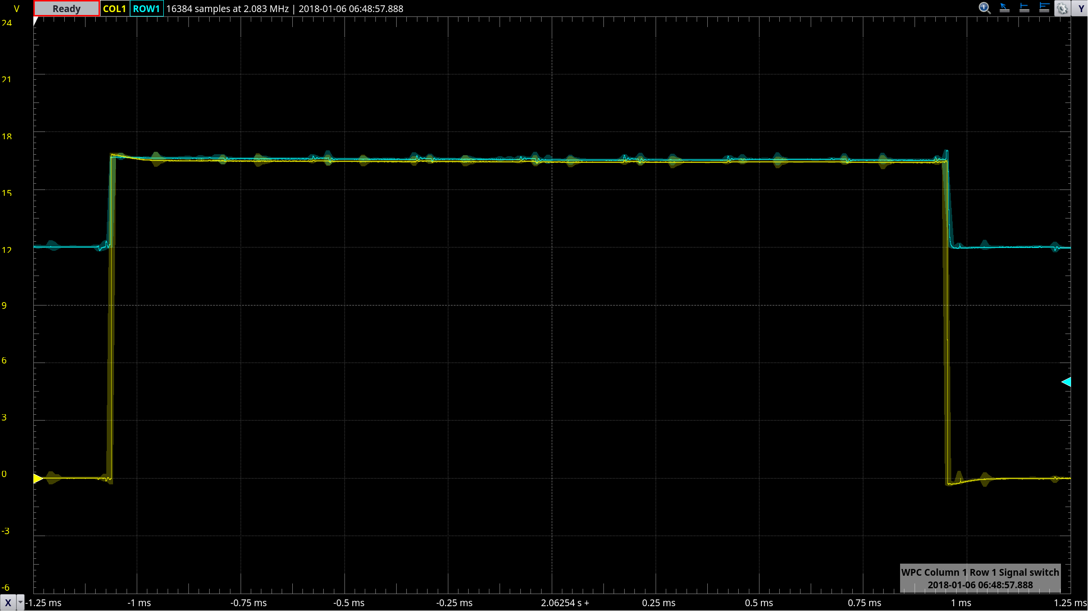
scopes/WPC/wh20_col1_row1.png
