bitfieldlabs/afterglow/scopes/WPC/wh20_col1_row1_off.png

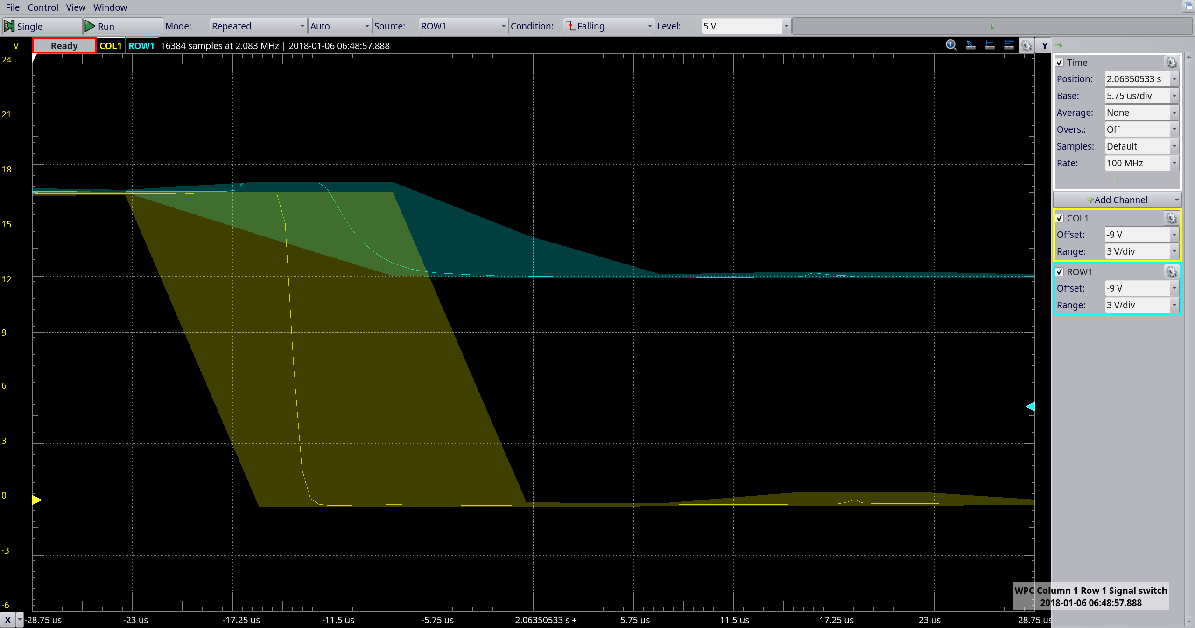
scopes/WPC/wh20_col1_row1_off.png
