bitfieldlabs/afterglow/scopes/WPC/wh20_col1_row1_on.png

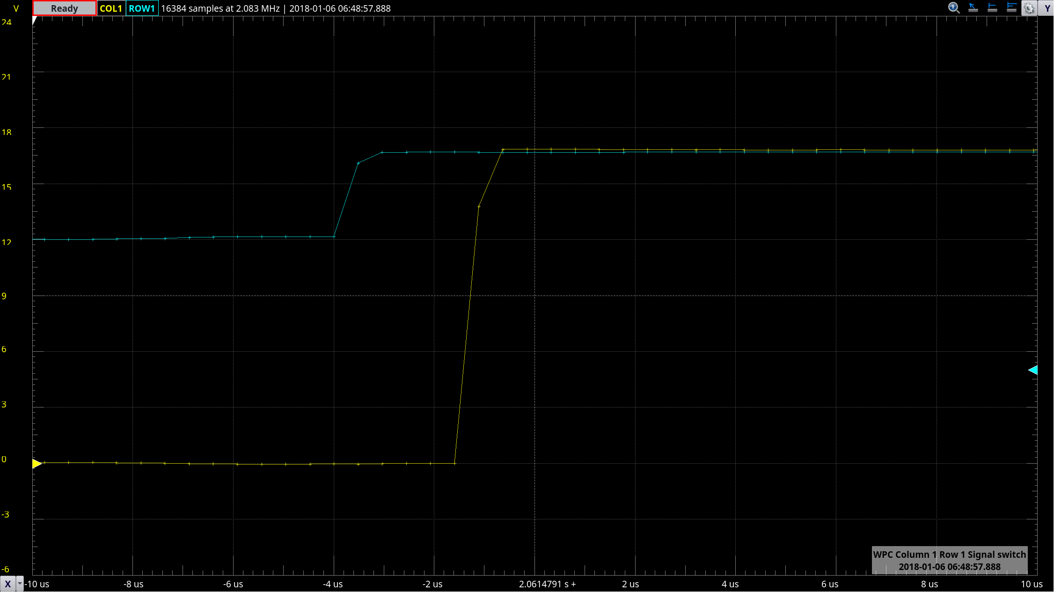
scopes/WPC/wh20_col1_row1_on.png
