bitfieldlabs/afterglow/scopes/WPC/wh20_incascendent_driving.png

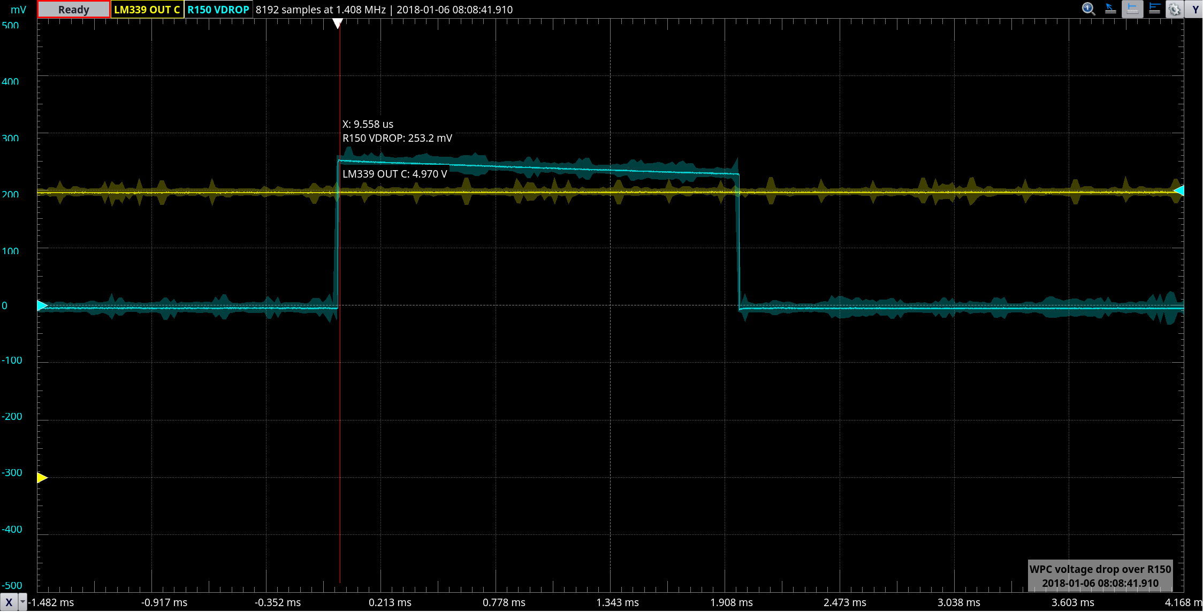
scopes/WPC/wh20_incascendent_driving.png
