bitfieldlabs/afterglow/scopes/AG/col1_col2_col1_testmode.png

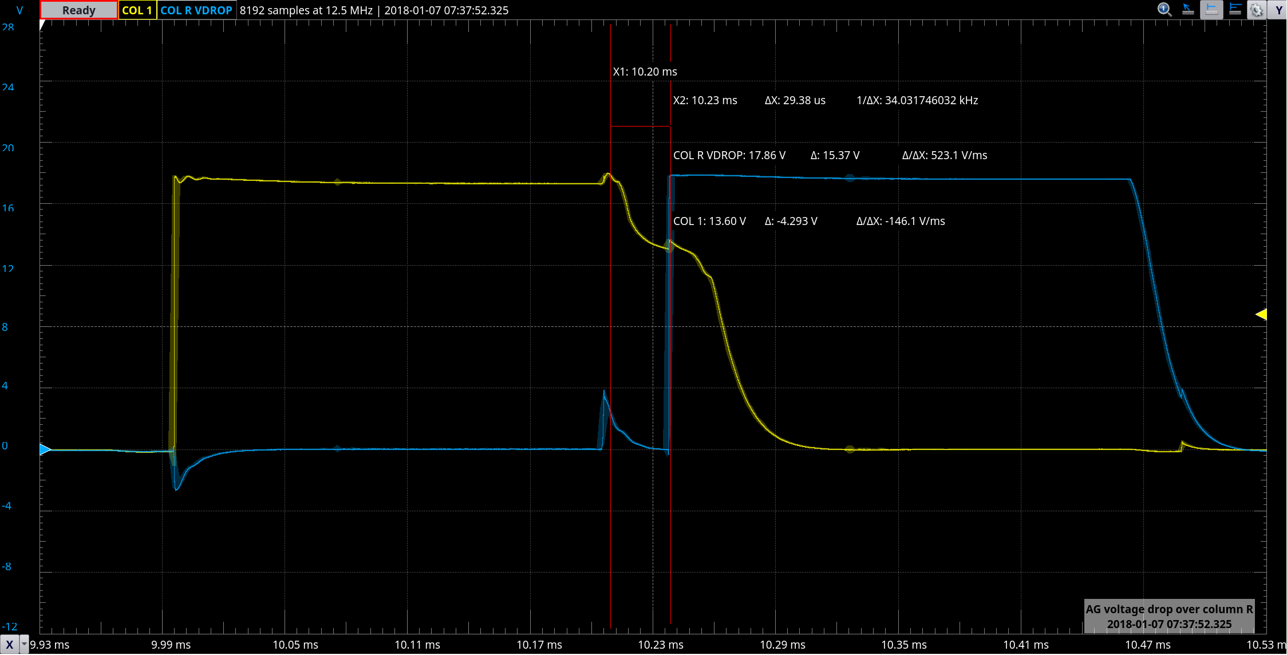
scopes/AG/col1_col2_col1_testmode.png
