bitfieldlabs/afterglow/scopes/AG/col1_col2_col2_testmode_full.png

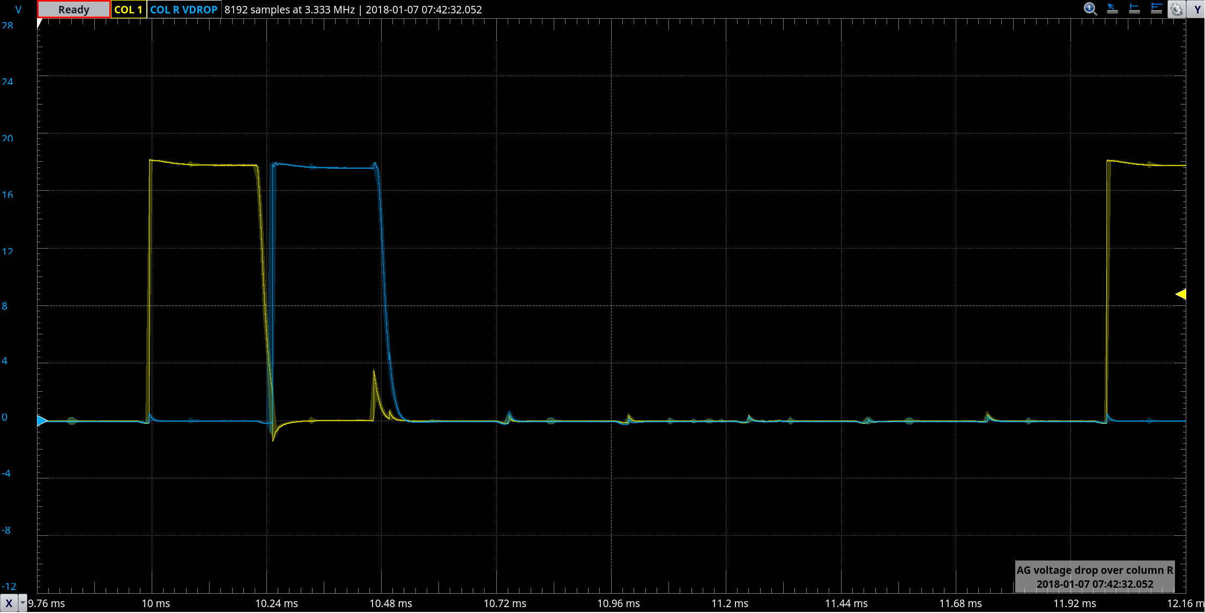
scopes/AG/col1_col2_col2_testmode_full.png
