bitfieldlabs/afterglow/scopes/current_over_R26_testmode.png

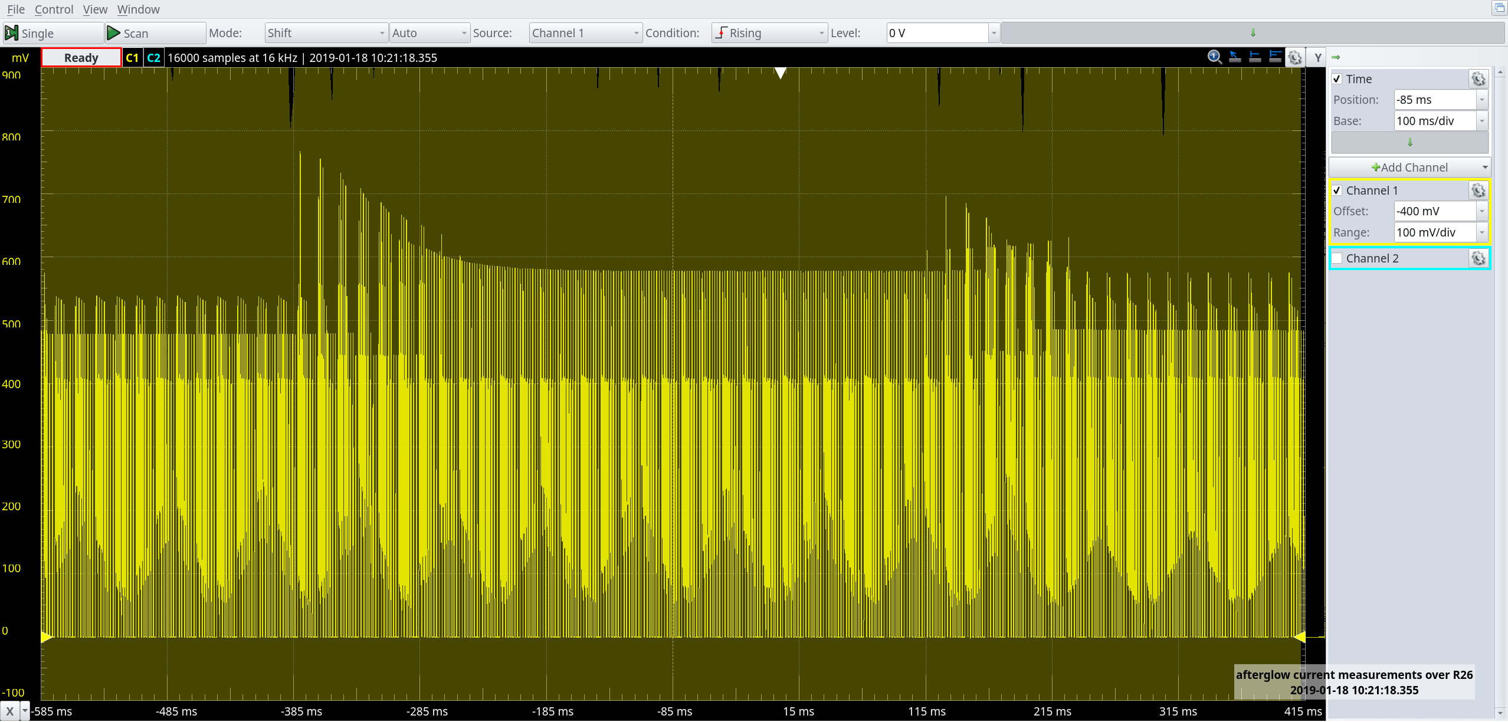
scopes/current_over_R26_testmode.png
