bitfieldlabs/afterglow/scopes/current_over_R26_testmode__col1_normal.png

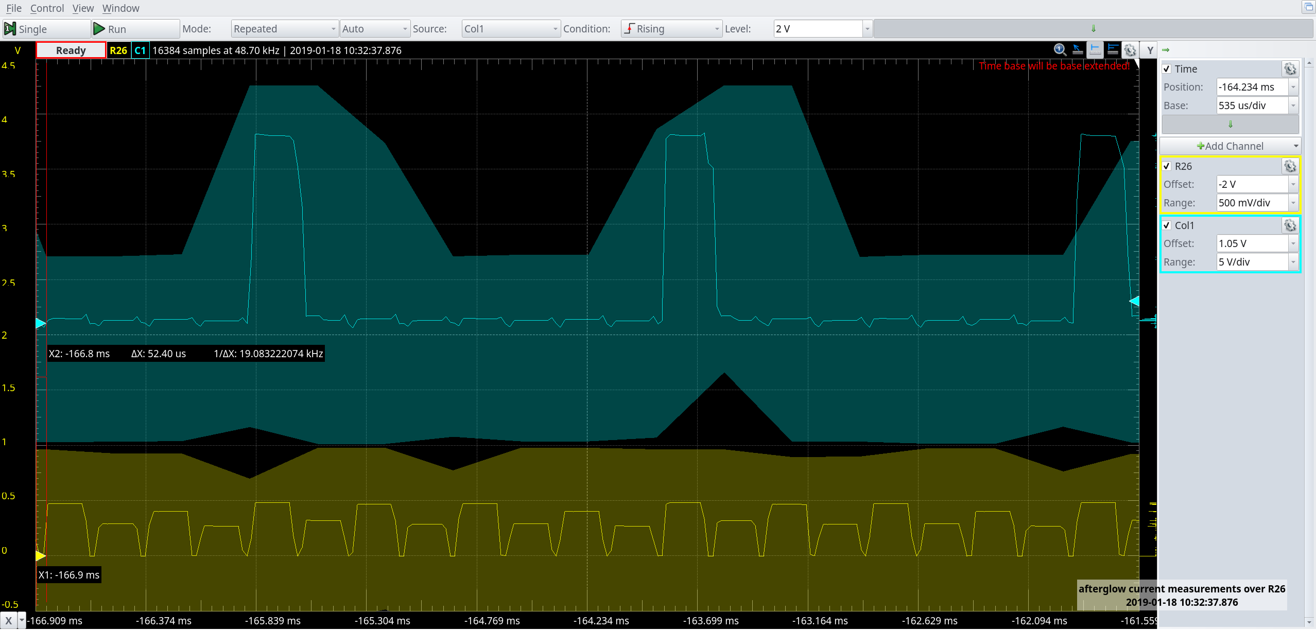
scopes/current_over_R26_testmode__col1_normal.png
