bitfieldlabs/afterglow/scopes/current_over_R26_testmode__col1_short_C1R6.png

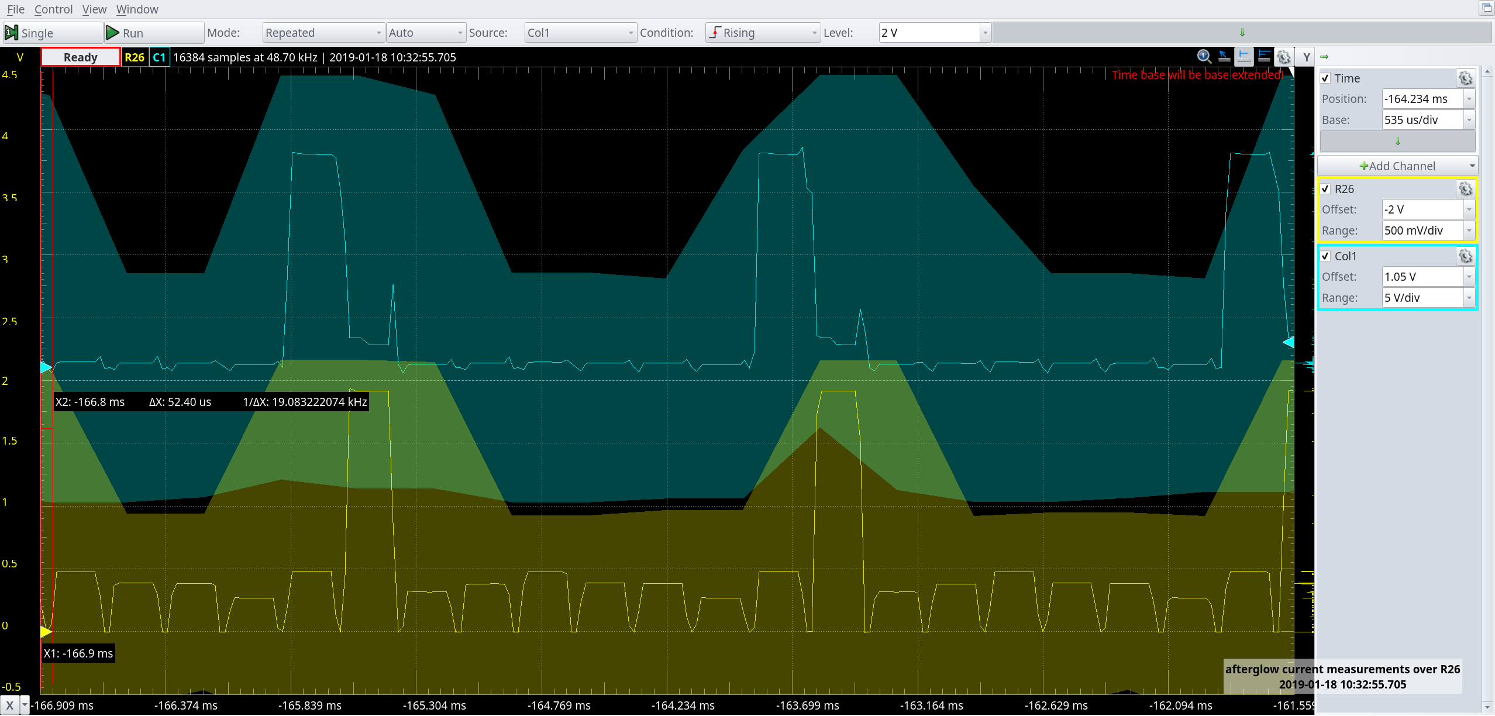
scopes/current_over_R26_testmode__col1_short_C1R6.png
