bitfieldlabs/afterglow/scopes/current_over_R26_testmode__col1_short_C2R7.png

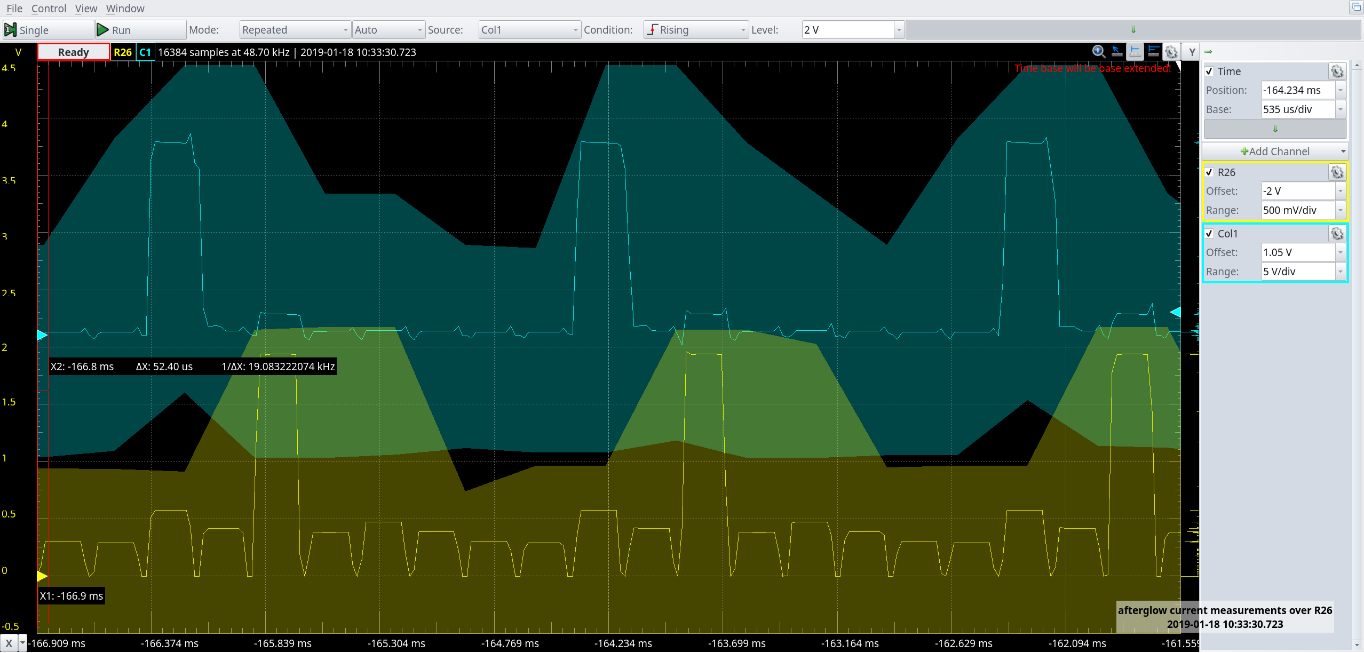
scopes/current_over_R26_testmode__col1_short_C2R7.png
