bitfieldlabs/afterglow/scopes/current_over_R26_testmode_zoom_1.png

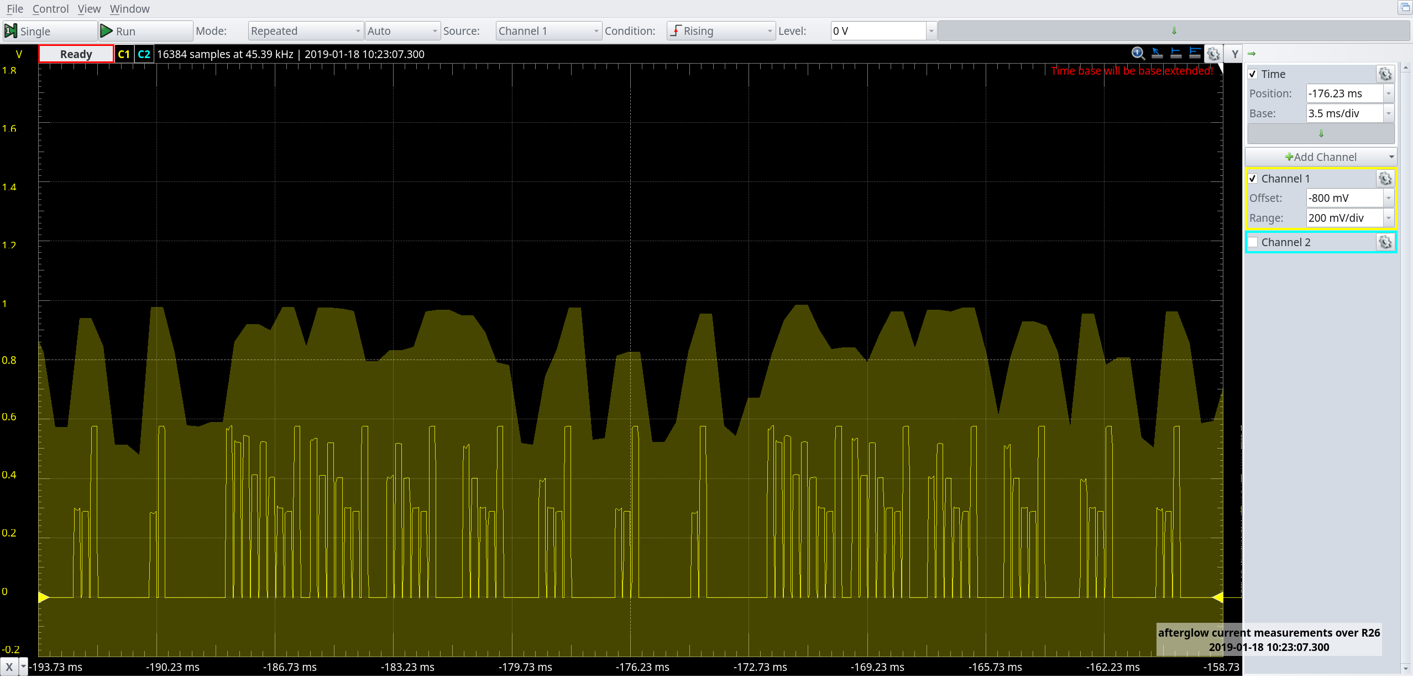
scopes/current_over_R26_testmode_zoom_1.png
