bitfieldlabs/afterglow/scopes/current_over_R26_testmode_zoom_3.png

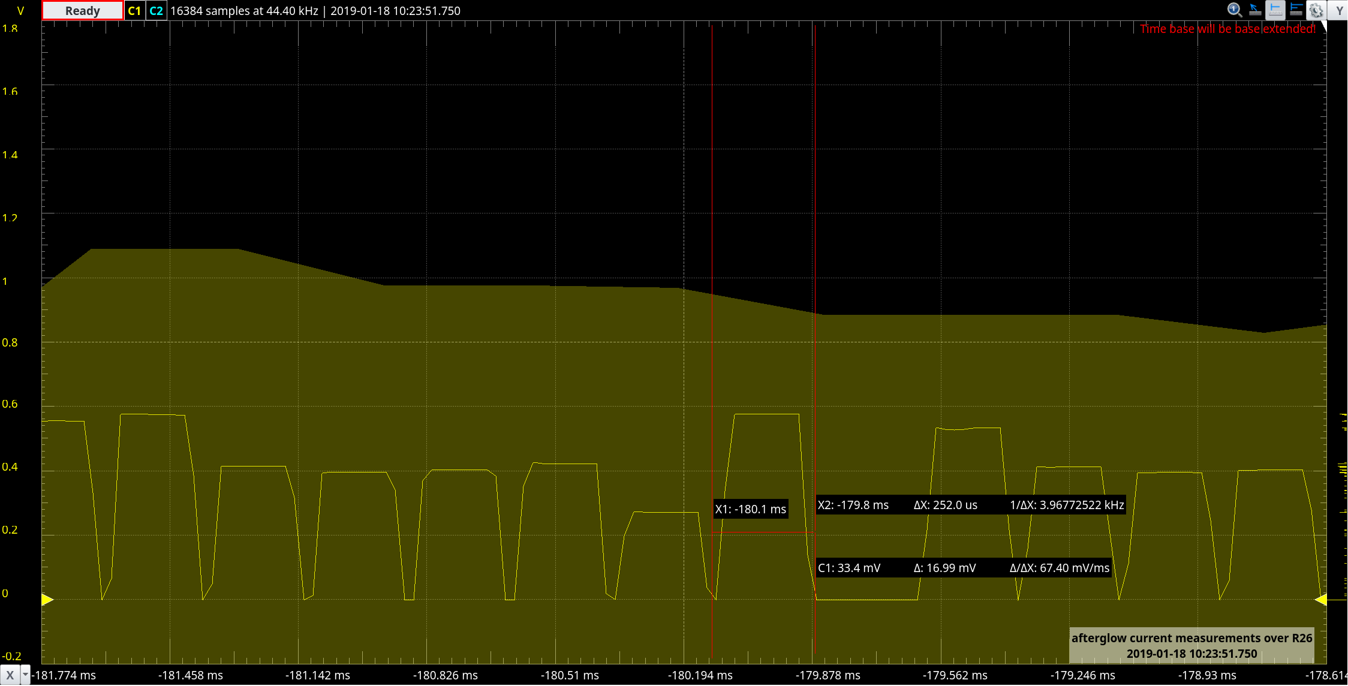
scopes/current_over_R26_testmode_zoom_3.png
