bitfieldlabs/afterglow/afterglow_rp2040_firmware/src/main.c

/***********************************************************************
 *   ___  ___  ___  ___  ___  ___   _    ___  _ _ _ 
 *  | . || __>|_ _|| __>| . \/  _> | |  | . || | | |
 *  |   || _>  | | | _> |   /| <_/\| |_ | | || | | |
 *  |_|_||_|   |_| |___>|_\_\`____/|___|`___'|__/_/ 
 *                                                 rp2040
 *      Copyright (c) 2024 bitfield labs
 *
 ***********************************************************************
 *  This file is part of the afterglow pinball LED project:
 *  https://github.com/bitfieldlabs/afterglow
 *
 *  Licensed under the Apache License, Version 2.0 (the "License");
 *  you may not use this file except in compliance with the License.
 *  You may obtain a copy of the License at:
 *
 *  https://www.apache.org/licenses/LICENSE-2.0
 *
 * Unless required by applicable law or agreed to in writing, software
 * distributed under the License is distributed on an "AS IS" BASIS,
 * WITHOUT WARRANTIES OR CONDITIONS OF ANY KIND, either express or implied.
 * See the License for the specific language governing permissions and
 * limitations under the License.
 ***********************************************************************/

/*

              +------CPU 0-----+       +------CPU 1-----+        +-------PIO------+


              +----------------+
              | main()         |
              |  + Setup       |
              |  | Status      |
              |  + Serial      |
              |                |
              +----------------+                                  LED update: 400Hz
                                                               PIO out: 128*8*400Hz
                     Timer 8 kHz                   100 Hz                    400kHz
              +----------------+       +----------------+        +----------------+
              | sample_input() |       | matrixout()    |        | matrixout PIO  |
              |                |       |                |        |                |
Col/Row +---->+  o raw matrix  +-------+  o brightness  +--------+  o PWM raw data|
Input         |    1bit        |       |    matrix      |        |    PWM_RES *   |
              |                |       |    16bits      |        |    NUM_COL     |
              |                |       |                |        |                |
              |.sRawLampMatrix |       |   .sLampMatrix |        |.sMatrixDataBuf1|
              |                |       |                |        |.sMatrixDataBuf2|
              +----------------+       +----------------+        +----------------+

              The input data is        The brightness ma-        The DMA pushes the
              sampled from the         trix is updated           prepared output buffer
              74HC165 shift re-        based on the raw          data to the PIO FIFO.
              gister and the raw       matrix data. The          The PIO simply outputs
              matrix is updated.       output data is pre-       the data directly to
                                       pared for the DMA         the associated GPIOs.
                                       in two output buffers     The DMA waits for the
                                       which are swapped         PIO to finish before
                                       whenever a new data       pushing new data.
                                       set has been prepared.
                                       These buffers consist
                                       of a full output pin
                                       state for each PWM
                                       frequency step
                                       (ledFreq * pwmRes * NUM_COL).
*/

#include <stdio.h>
#include "pico/stdlib.h"
#include "pico/multicore.h"
#include "hardware/watchdog.h"
#include "hardware/adc.h"
#include "pindef.h"
#include "lampmatrix.h"
#include "matrixout.h"
#include "serial.h"
#include "afterglow.h"
#include "config.h"
#include "params.h"
#include "display.h"
#include "record.h"
#include "smart.h"
#if MODDING_OUTPUT
#include "mod.h"
#endif


//------------------------------------------------------------------------------
// local variables

// The timer is the trigger for the input sampling and the matrix update
static repeating_timer_t sInputSamplingTimer;
static volatile uint32_t sTtag = 0;
static uint32_t sMatrixUpdateCounter = 0;
static AG_DIPSWITCH_t sLastDIPSwitch = { 0 };


//------------------------------------------------------------------------------
// local functions

void checkForConfigChanges();


//------------------------------------------------------------------------------
bool sample_input(struct repeating_timer *t)
{
    // sample and process the the inputs
    lm_inputUpdate(sTtag);

    // trigger an update of the output data
    if (sMatrixUpdateCounter == 0)
    {
        // send the current matrix state to the thread on CPU1
        if (!record_active())
        {
            multicore_fifo_push_blocking((uint32_t)lm_rawLampMatrix());
        }

        // restart the update counter
        sMatrixUpdateCounter = SAMPLE_TO_UPDATE_RATIO;
    }
    else
    {
        // no matrix update this time
        sMatrixUpdateCounter--;
    }

    // time is ticking
    sTtag++;

    return true;
}

//------------------------------------------------------------------------------
void panic_mode()
{
    // endless panic
    while (true)
    {
        // blinking alert
        gpio_put(AGPIN_STAT_LED, 1);
        sleep_ms(200);
        gpio_put(AGPIN_STAT_LED, 0);
        sleep_ms(200);
    }
}

//------------------------------------------------------------------------------
int main(void)
{
    stdio_usb_init();
    stdio_init_all();

    // initialize the status LED
    gpio_init(AGPIN_STAT_LED);
    gpio_set_dir(AGPIN_STAT_LED, GPIO_OUT);

    // data input pin
    gpio_init(AGPIN_IN_DATA);
    gpio_set_dir(AGPIN_IN_DATA, GPIO_IN);
    gpio_set_pulls(AGPIN_IN_DATA, true, false); // pull up

    // output pins
    for (uint32_t p=0; p<NUM_COL_PINS; p++)
    {
        uint pin = skAGColOutPins[p];
        gpio_init(pin);
        gpio_put(pin, false);
        gpio_set_dir(pin, GPIO_OUT);
    }
    for (uint32_t p=0; p<NUM_ROW_PINS; p++)
    {
        uint pin = skAGRowOutPins[p];
        gpio_init(pin);
        gpio_put(pin, false);
        gpio_set_dir(pin, GPIO_OUT);
    }
    gpio_init(AGPIN_OUT_CLK);
    gpio_put(AGPIN_OUT_CLK, false);
    gpio_set_dir(AGPIN_OUT_CLK, GPIO_OUT);
    gpio_init(AGPIN_OUT_DATA);
    gpio_put(AGPIN_OUT_DATA, false);
    gpio_set_dir(AGPIN_OUT_DATA, GPIO_OUT);
    gpio_init(AGPIN_OUT_LOAD);
    gpio_put(AGPIN_OUT_LOAD, false);
    gpio_set_dir(AGPIN_OUT_LOAD, GPIO_OUT);

    gpio_init(AGPIN_IN_CLK);
    gpio_put(AGPIN_IN_CLK, false);
    gpio_set_dir(AGPIN_IN_CLK, GPIO_OUT);
    gpio_init(AGPIN_IN_LOAD);
    gpio_put(AGPIN_IN_LOAD, false);
    gpio_set_dir(AGPIN_IN_LOAD, GPIO_OUT);

    gpio_init(AGPIN_D_SCL);
    gpio_put(AGPIN_D_SCL, false);
    gpio_set_dir(AGPIN_D_SCL, GPIO_OUT);
    gpio_init(AGPIN_D_SDA);
    gpio_put(AGPIN_D_SDA, false);
    gpio_set_dir(AGPIN_D_SDA, GPIO_OUT);

#if DEBUG_OLED_I2C
    // i2c display
    bool dispInit = display_init();
#endif

    // ADC initialisation
    adc_init();
    adc_select_input(0); // GPIO26 -> current measurement

    // configuration initialisation
    cfg_init();
    sLastDIPSwitch = cfg_dipSwitch();

    // Active test moe *and* replay mode indicate record mode -
    // initialize recording storage
    if (sLastDIPSwitch.testMode && sLastDIPSwitch.replayMode)
    {
        record_init();
    }

    // parameters initialisation
    par_setDefault();

    // lamp matrix initialisation
    lm_init();

    // try to identify incandescent lamps and shorts
    if (sLastDIPSwitch.smartMode)
    {
        smart_detect_lamps();
    }

    if (!sLastDIPSwitch.passThrough)
    {
        // set up the matrix output DMA and PIO
        if (!matrixout_initpio())
        {
            panic_mode();
        }
    }

    // prepare the brightness steps
    matrixout_prepareBrightnessSteps();

    // start a thread on CPU1, used either for matrix data preparation
    // or for full-speed pass-through
    multicore_launch_core1(matrixout_thread);

    // Input sampling setup
    if (!sLastDIPSwitch.passThrough)
    {
        if (!add_repeating_timer_us(-INPUT_SAMPLE_INT, sample_input, NULL, &sInputSamplingTimer))
        {
            printf("Failed to start the input handler timer!\n");
            panic_mode();
        }
    }

    // enable serial output at 115200 baudrate
    printf("afterglow rp2040 v%d  (c) 2024 bitfield labs\n", AFTERGLOW_RP2040_VERSION);
    if (watchdog_caused_reboot())
    {
        printf("Watchdog reboot!\n");
    }
#if DEBUG_OLED_I2C
    printf("%s", dispInit ? "OLED display detected\n" : "No display detected\n");
#endif

    // enable a 1s watchdog
    watchdog_enable(1000, 1);

    // Eternal loop
    uint32_t c = 0;
    while (true)
    {
        // kick the dog
        watchdog_update();

        // handle configuration changes
        checkForConfigChanges();

        // afterglow serial communication
        serial_comm(sTtag);

        // status update
        ag_statusUpdate();

        // display update
        display_update();

#if MODDING_OUTPUT
        //  evaluate the modding logic and update the pins
        mod_evaluate();
        mod_output();
#endif

        // time for a nap
        sleep_ms(50);
    }
}

//------------------------------------------------------------------------------
void checkForConfigChanges()
{
    AG_DIPSWITCH_t dipSwitch = cfg_dipSwitch();

    // Pass-through configuration changes
    if (dipSwitch.passThrough != sLastDIPSwitch.passThrough)
    {
        // reboot, the new mode will be applied at startup
        watchdog_reboot(0, 0, 0);
    }

    // check for record mode start
    // (deactivating test mode while replay mode is on)
    if (dipSwitch.replayMode && sLastDIPSwitch.replayMode &&
        !dipSwitch.testMode && sLastDIPSwitch.testMode)
    {
        // start recording
        record_start();
    }

    // Serial port configuration
    if (cfg_newConfigAvailable())
    {
        // apply the new configuration and store it to flash
        if (cfg_applyNewConfig())
        {
#if DEBUG_SERIAL
            printf("Cfg saved to flash");
#endif
        }

        matrixout_prepareBrightnessSteps();
    }

    sLastDIPSwitch = dipSwitch;
}
