bitfieldlabs/afterglow/afterglow_rp2040_firmware/src/matrixout.c

/***********************************************************************
 *   ___  ___  ___  ___  ___  ___   _    ___  _ _ _ 
 *  | . || __>|_ _|| __>| . \/  _> | |  | . || | | |
 *  |   || _>  | | | _> |   /| <_/\| |_ | | || | | |
 *  |_|_||_|   |_| |___>|_\_\`____/|___|`___'|__/_/ 
 *                                                 rp2040
 *      Copyright (c) 2024 bitfield labs
 *
 ***********************************************************************
 *  This file is part of the afterglow pinball LED project:
 *  https://github.com/bitfieldlabs/afterglow
 *
 *  Licensed under the Apache License, Version 2.0 (the "License");
 *  you may not use this file except in compliance with the License.
 *  You may obtain a copy of the License at:
 *
 *  https://www.apache.org/licenses/LICENSE-2.0
 *
 * Unless required by applicable law or agreed to in writing, software
 * distributed under the License is distributed on an "AS IS" BASIS,
 * WITHOUT WARRANTIES OR CONDITIONS OF ANY KIND, either express or implied.
 * See the License for the specific language governing permissions and
 * limitations under the License.
 ***********************************************************************/

#include <string.h>
#include "matrixout.h"
#include "pico/multicore.h"
#include "pico/time.h"
#include "hardware/gpio.h"
#include "hardware/pio.h"
#include "hardware/dma.h"
#include "hardware/watchdog.h"
#include "def.h"
#include "pindef.h"
#include "matrixout.pio.h"
#include "afterglow.h"
#include "bmap.h"
#include "config.h"
#include "params.h"
#include "input.h"
#include "pindef.h"
#include "record.h"
#include "smart.h"


//------------------------------------------------------------------------------
// Local data

// Matrix output on PIO 0
static PIO sPioMatrixOut = pio0;
static int sSmMatrixOut = -1;
static int sSmMatrixOutOffset = -1;

static int sDMAChan = -1;
static dma_channel_config sDMAChanConfig;

// The final lamp brightness matrix
static uint32_t sLampMatrix[NUM_COL][NUM_ROW] = { 0 };

// The final lamp on/off time matrix
static uint32_t sLampMatrixOntime[NUM_COL][NUM_ROW] = { 0 };
static uint32_t sLampMatrixOfftime[NUM_COL][NUM_ROW] = { 0 };
static uint32_t sLampMatrixOffDelay[NUM_COL][NUM_ROW] = { 0 };

// The lamp brightness steps matrix
static uint32_t sLampMatrixStepsOn[NUM_COL][NUM_ROW] = { 0 };
static uint32_t sLampMatrixStepsOff[NUM_COL][NUM_ROW] = { 0 };

// The lamp maximum brightness matrix
static uint32_t sLampMatrixMaxBr[NUM_COL][NUM_ROW] = { 0 };

// local lamp matrix copy
static uint32_t sLampMatrixCopy[NUM_COL] = { 0 };

// use double buffering for the prepared output data
static uint32_t sMatrixDataBuf1[NUM_COL*PWM_RES_MAX*2] = { 0 };
static uint32_t sMatrixDataBuf2[NUM_COL*PWM_RES_MAX*2] = { 0 };
static volatile uint32_t *pMatrixDataBufOut = sMatrixDataBuf1;
static volatile uint32_t *pMatrixDataBufPrep = sMatrixDataBuf2;

// maximum duration of matrix update
static uint32_t sMaxDur = 0;

// local copy of the recording buffer
static uint32_t sRecordBufCopy[REC_RAMBUF_SIZE] = { 0 };


//------------------------------------------------------------------------------
// local functions

void matrixout_prepareCol(uint col, uint8_t *pRowDur);
void matrixout_prepareData(const uint32_t *pkLM);
void matrixout_swapbuf();
void matrixout_updateLampMatrix(const uint32_t *pkRawLM);


//------------------------------------------------------------------------------
void matrixout_thread()
{
    // initialize the data
    memset(sLampMatrix, 0, sizeof(sLampMatrix));
    memset(sLampMatrixOntime, 0, sizeof(sLampMatrixOntime));
    memset(sLampMatrixOfftime, 0, sizeof(sLampMatrixOfftime));
    memset(sLampMatrixOffDelay, 0, sizeof(sLampMatrixOffDelay));

    // prepare the brightness steps matrix
    matrixout_prepareBrightnessSteps();

    AG_DIPSWITCH_t ds = cfg_dipSwitch();

    if (!ds.passThrough)
    {
        // Afterglow mode: matrix preparation thread
        while (true)
        {
            // wait until CPU0 triggers the data output preparation
            const uint32_t *pkData = (const uint32_t*)multicore_fifo_pop_blocking();

            // time is ticking
            uint64_t ts = to_us_since_boot(get_absolute_time());

            // in record mode this is actually a request to write data to flash
            if (record_isrecdata((const uint8_t*)pkData))
            {
                // make a copy of the data
                memcpy(sRecordBufCopy, pkData, sizeof(sRecordBufCopy));

                // write to flash
                record_write_flash((const uint8_t*)sRecordBufCopy, sizeof(sRecordBufCopy));
            }
            else
            {
                // make a local copy of the raw map matrix
                memcpy(sLampMatrixCopy, pkData, sizeof(sLampMatrixCopy));

                // update the lamp brightness matrix based on the new raw matrix data
                matrixout_updateLampMatrix(sLampMatrixCopy);

                // prepare the PIO buffer
                matrixout_prepareData(&sLampMatrix[0][0]);
            }

            // measure time
            uint64_t te = to_us_since_boot(get_absolute_time());
            uint32_t dur = (uint32_t)(te - ts);
            if (dur > sMaxDur)
            {
                sMaxDur = dur;
            }
        }
    }
    else
    {
        // Pass-through mode: full speed data in- and output
        while (true)
        {
            // time is ticking
            uint64_t ts = to_us_since_boot(get_absolute_time());

            // read the input
            uint32_t dataIn = input_dataRead();

            // process the DIP switch information (bits 19-23 of the input)
            // Bits 0-3: CFG1 - CFG4
            cfg_updateDipSwitch((uint8_t)((dataIn>>18) & 0x0f));

            // replicate the input at the output pins
            uint32_t outData = (dataIn & 0x000000ff); // 8 column bits
            outData |= ((~dataIn) & 0x0003ff00); // 10 row bits, invert the row data, inputs HIGH are OFF
            gpio_clr_mask((~outData) & 0x0003ffff);
            gpio_set_mask(outData);

            // measure time
            uint64_t te = to_us_since_boot(get_absolute_time());
            uint32_t dur = (uint32_t)(te - ts);
            if (dur > sMaxDur)
            {
                sMaxDur = dur;
            }
        }

    }
}

//------------------------------------------------------------------------------
void matrixout_swapbuf()
{
    // swap between the two output data buffers
    if (pMatrixDataBufPrep == sMatrixDataBuf1)
    {
        pMatrixDataBufOut = sMatrixDataBuf1;
        pMatrixDataBufPrep = sMatrixDataBuf2;
    }
    else
    {
        pMatrixDataBufOut = sMatrixDataBuf2;
        pMatrixDataBufPrep = sMatrixDataBuf1;
    }
}

//------------------------------------------------------------------------------
void matrixout_prepareData(const uint32_t *pkLM)
{
    // No output with invalid data
    AFTERGLOW_STATUS_t s = ag_status();
    if ((s != AG_STATUS_INIT) && (s != AG_STATUS_INVINPUT))
    {
        AG_DIPSWITCH_t dipSwitch = cfg_dipSwitch();
        uint8_t rowDur[NUM_ROW];

        // process column by column
        for (uint c=0; c<NUM_COL; c++)
        {
            uint8_t *pRD = rowDur;
            for (uint r=0; r<NUM_ROW; r++, pkLM++, pRD++)
            {
                // decimate the lamp brightness value to 8 bits
                uint8_t rb = (uint8_t)(*pkLM >> 24);

                // map the brightness value
                if (true)
                {
                    // use the brightness map
                    const AG_PARAMS_t *pkPar = par_params();
                    *pRD = pkPar->pkBrightnessMap[rb];
                }
                else
                {
                    // linear brightness value
                    *pRD = rb;
                }
            }

            // prepare the output data
            matrixout_prepareCol(c, rowDur);
        }
    }
    else
    {
        memset(pMatrixDataBufPrep, 0, sizeof(sMatrixDataBuf1));
    }

    // swap the output/prepare buffers (double buffering)
    matrixout_swapbuf();
}

//------------------------------------------------------------------------------
void matrixout_prepareCol(uint col, uint8_t *pRowDur)
{
    const AG_PARAMS_t *pkPar = par_params();

    // Anti-ghosting: turn off everything for some time
    // No need to do anything here - sMatrixDataBuf has already an empty buffer
    // of ANTI_GHOSTING_STEPS entries at the beginning

    // prepare the column and row data for all PWM steps
    uint32_t rbit = 0x00000100;
    uint32_t colBit = (1ul << col);
    uint32_t *pDS = &pMatrixDataBufPrep[col*pkPar->matrixPIOSteps+pkPar->antiGhostSteps];
    uint32_t *pD = pDS;
    for (uint s=0; s<PWM_RES; s++)
    {
        *pD++ = colBit;
    }
    for (uint r=0; r<NUM_ROW; r++)
    {
        uint rd = *pRowDur;
        pD = pDS;
        uint32_t rbitm = ~rbit;
        uint s = rd;
        while (s--)
        {
            *pD |= rbit;
            pD++;
        }
        s = (PWM_RES-rd);
        while (s--)
        {
            *pD &= rbitm;
            pD++;
        }
        pRowDur++;
        rbit <<= 1;
    }
}

//------------------------------------------------------------------------------
void matrix_transfer_complete()
{
    // clear the interrupt request
    dma_hw->ints0 = (1u << sDMAChan);

    // set the buffer address and retrigger
    dma_channel_set_read_addr(sDMAChan, pMatrixDataBufOut, true);
}

//------------------------------------------------------------------------------
bool matrixout_initpio()
{
    const AG_PARAMS_t *pkPar = par_params();

    // find a place for the PIO program in the instruction memory
    if (sSmMatrixOutOffset == -1)
    {
        sSmMatrixOutOffset = pio_add_program(sPioMatrixOut, &matrixout_program);
    }
    // claim an unused state machine for the matrix output and run the program
    if (sSmMatrixOut == -1)
    {
        sSmMatrixOut = pio_claim_unused_sm(sPioMatrixOut, true);
    }
    matrixout_program_init(sPioMatrixOut, sSmMatrixOut, sSmMatrixOutOffset);

    // claim and configure a free dma channel
    if (sDMAChan == -1)
    {
        sDMAChan = dma_claim_unused_channel(false);
    }
    sDMAChanConfig = dma_channel_get_default_config(sDMAChan);
    channel_config_set_transfer_data_size(&sDMAChanConfig, DMA_SIZE_32);
    channel_config_set_read_increment(&sDMAChanConfig, true);    // Read pointer increments with every step
    channel_config_set_write_increment(&sDMAChanConfig, false);  // Write pointer always points to PIO FIFO
    channel_config_set_dreq(&sDMAChanConfig, pio_get_dreq(sPioMatrixOut, sSmMatrixOut, true));  // Wait for the PIO to finish before writing

    dma_channel_configure(
        sDMAChan,                           // channel to be configured
        &sDMAChanConfig,                    // the channel's configuration
        &sPioMatrixOut->txf[sSmMatrixOut],  // write to the PIO TX FIFO
        NULL,                               // the read address will be set later
        pkPar->matrixPIOSteps*NUM_COL,      // number of transfers
        false                               // don't start yet
    );

    // raise IRQ 0 when the transfer finishes
    dma_channel_set_irq0_enabled(sDMAChan, true);
    irq_set_exclusive_handler(DMA_IRQ_0, matrix_transfer_complete);
    irq_set_enabled(DMA_IRQ_0, true);

    // start the infinite loop
    matrix_transfer_complete();

    return ((sSmMatrixOut != -1) && (sDMAChan != -1));
}

//------------------------------------------------------------------------------
void matrixout_stoppio()
{
    // stop the DMA
    dma_channel_abort(sDMAChan);

    // stop the PIO
    pio_sm_set_enabled(sPioMatrixOut, sSmMatrixOut, false);

    // set all output LOW
    gpio_put_masked(AGPIN_OUT_ALL_MASK, false);
}

//------------------------------------------------------------------------------
void matrixout_updateLampMatrix(const uint32_t *pkRawLM)
{
    const AFTERGLOW_CFG_t *pkCfg = cfg_config();
    const AG_PARAMS_t *pkPar = par_params();
    for (uint c=0; c<NUM_COL; c++)
    {
        uint32_t rowBit = 0x01;
        for (uint r=0; r<NUM_ROW; r++)
        {
            // Increase or decrease the lamp brightness value depedning on its
            // current state in the raw matrix.
            if ((*pkRawLM) & rowBit)
            {
                // increase brightness
                if (sLampMatrixOntime[c][r] >= pkCfg->lampDelay[c][r])
                {
                    if (sLampMatrix[c][r] < (sLampMatrixMaxBr[c][r] - sLampMatrixStepsOn[c][r]))
                    {
                        sLampMatrix[c][r] += sLampMatrixStepsOn[c][r];
                    }
                    else
                    {
                        sLampMatrix[c][r] = sLampMatrixMaxBr[c][r];
                    }
                }
                sLampMatrixOntime[c][r] += pkPar->matrixUpdateIntMs;
                sLampMatrixOfftime[c][r] = 0;
                sLampMatrixOffDelay[c][r] = 0;
            }
            else
            {

                if (sLampMatrixOffDelay[c][r] > 0)
                {
                    if (sLampMatrixOffDelay[c][r] > pkPar->matrixUpdateIntMs)
                    {
                        sLampMatrixOffDelay[c][r] -= pkPar->matrixUpdateIntMs;
                    }
                    else
                    {
                        sLampMatrixOffDelay[c][r] = 0;
                    }
                }
                if ((sLampMatrixOfftime[c][r] == 0) &&
                    (ag_mode() == AG_MODE_WHITESTAR) && (sLampMatrixOntime[c][r] < 32))
                {
                    // Turn lamps off with some delay to allow for dimming
                    // with short on-times
                    sLampMatrixOffDelay[c][r] = 22;
                }

                if (sLampMatrixOfftime[c][r] >= sLampMatrixOffDelay[c][r])
                {
                    // decrease brightness
                    if (sLampMatrix[c][r] > sLampMatrixStepsOff[c][r])
                    {
                        sLampMatrix[c][r] -= sLampMatrixStepsOff[c][r];
                    }
                    else
                    {
                        sLampMatrix[c][r] = 0;
                    }
                }
                sLampMatrixOfftime[c][r] += pkPar->matrixUpdateIntMs;
                sLampMatrixOntime[c][r] = 0;
            }
            rowBit <<= 1;
        }
        pkRawLM++;
    }
}

//------------------------------------------------------------------------------
void matrixout_prepareBrightnessSteps()
{
    // Prepare the brightness increase/decrease values per matrix update for
    // each lamp in the maxtrix. This value will be added in each update step if
    // the lamp is on in the raw matrix, and it will be subtracted from the
    // current brightness if the lamp is off.
    // The brightness is linear in the matrix, it will be translated to
    // non-linear PWM steps when preparing the PWM data.
    // This is the magic sauce for the afterglow effect.
    const AFTERGLOW_CFG_t *pkCfg = cfg_config();
    const AG_PARAMS_t *pkPar = par_params();
    for (uint c=0; c<NUM_COL; c++)
    {
        for (uint r=0; r<NUM_ROW; r++)
        {
            // keep the dog alive
            watchdog_update();

            // configured glow duration for this lamp [us]
            uint32_t gdOn = (pkCfg->lampGlowDurOn[c][r] * GLOWDUR_CFG_SCALE) * 1000;           
            uint32_t gdOff = (pkCfg->lampGlowDurOff[c][r] * GLOWDUR_CFG_SCALE) * 1000;

            // maximum brightness (32 bits), 8 steps only
            uint32_t maxBr = ((uint32_t)0xffffffff >> 3) * (uint32_t)(pkCfg->lampBrightness[c][r] + 1);
            double agRatio = ((double)PWM_RES / (double)pkPar->matrixPIOSteps);
            maxBr = (uint32_t)((double)maxBr * agRatio);
            sLampMatrixMaxBr[c][r] = maxBr;

            // override lamp duration in smart mode
            if (cfg_dipSwitch().smartMode)
            {
                LAMP_TYPE_t lt = smart_lampType(c, r);
                // no afterglow needed for incandescents
                if (lt == LAMP_TYPE_INC)
                {
                    gdOn = 0;
                    gdOff = 0;
                }
                // disable output for shorts
                else if  (lt == LAMP_TYPE_SHORT)
                {
                    sLampMatrixMaxBr[c][r] = 0;
                }
            }

            // account for the configured lamp delay
            uint32_t ld = (pkCfg->lampDelay[c][r] * 1000);
            gdOn = (ld < gdOn) ? (gdOn - ld) : 0;

            // calculate the step size for this lamp
            float numStepsOn = ((float)gdOn / (float)pkPar->matrixUpdateInt);
            float numStepsOff = ((float)gdOff / (float)pkPar->matrixUpdateInt);
            if (numStepsOn < 1.0f) numStepsOn  = 1.0f;
            if (numStepsOff < 1.0f) numStepsOff  = 1.0f;
            sLampMatrixStepsOn[c][r] = (uint32_t)((float)maxBr / numStepsOn);
            sLampMatrixStepsOff[c][r] = (uint32_t)((float)maxBr / numStepsOff);

            //printf("ST %d %d %lu %lu %lu\n", c, r, sLampMatrixMaxBr[c][r], sLampMatrixStepsOn[c][r], sLampMatrixStepsOff[c][r]);
        }
    }
}

//------------------------------------------------------------------------------
const uint32_t * matrixout_lampMatrix()
{
    return &sLampMatrix[0][0];
}

//------------------------------------------------------------------------------
uint32_t matrixout_updateMaxDurAndClear()
{
    uint32_t maxDur = sMaxDur;
    sMaxDur = 0;
    return maxDur;
}
