bitfieldlabs/afterglow/afterglow_rp2040_firmware/src/record.c

/***********************************************************************
 *   ___  ___  ___  ___  ___  ___   _    ___  _ _ _ 
 *  | . || __>|_ _|| __>| . \/  _> | |  | . || | | |
 *  |   || _>  | | | _> |   /| <_/\| |_ | | || | | |
 *  |_|_||_|   |_| |___>|_\_\`____/|___|`___'|__/_/ 
 *                                                 rp2040
 *      Copyright (c) 2024 bitfield labs
 *
 ***********************************************************************
 *  This file is part of the afterglow pinball LED project:
 *  https://github.com/bitfieldlabs/afterglow
 *
 *  Licensed under the Apache License, Version 2.0 (the "License");
 *  you may not use this file except in compliance with the License.
 *  You may obtain a copy of the License at:
 *
 *  https://www.apache.org/licenses/LICENSE-2.0
 *
 * Unless required by applicable law or agreed to in writing, software
 * distributed under the License is distributed on an "AS IS" BASIS,
 * WITHOUT WARRANTIES OR CONDITIONS OF ANY KIND, either express or implied.
 * See the License for the specific language governing permissions and
 * limitations under the License.
 ***********************************************************************/

#include <string.h>
#include "record.h"
#include "pico/stdlib.h"
#include "hardware/flash.h"
#include "pico/multicore.h"
#include "display.h"


//------------------------------------------------------------------------------
// Recording storage definitions

// recording magic marker
#define REC_MAGIC 0x50524741

// recording header size [bytes]
#define REC_HEADER_SIZE 8

// Use a flash region 256kb from the flash start for storing the recording
#define REC_FLASH_OFFSET (256 * 1024)

// Record size (900 * 4096b = 3.7Mb, records around two minutes of data)
#define REC_FLASH_SIZE (900 * FLASH_SECTOR_SIZE)

// Pointer to the record storage
const uint8_t *pkFlashRec = (const uint8_t *) (XIP_BASE + REC_FLASH_OFFSET);

// header information
typedef struct REC_HEADER_s
{
    uint32_t magic;     // magic word
    uint32_t size;      // recording size [bytes]
} REC_HEADER_t;


//------------------------------------------------------------------------------
// local variables

// data buffer in RAM (double buffering)
static uint32_t sDataBuffer[REC_RAMBUF_SIZE*2] = { 0 };

static uint32_t sRamBufPos = 0;
static uint32_t sReplayPos = 0;
static uint32_t sFlashPos = 0;
static bool sRecordActive = false;
static bool sRecordInit = false;
static bool sRecordInitStarted = false;


//------------------------------------------------------------------------------
void record_init()
{
    // erase the record sectors
    sRecordInitStarted =  true;
    display_setNotice("RECORD", "Erasing flash", "...", 2000000);
    display_update();
    flash_range_erase(REC_FLASH_OFFSET, REC_FLASH_SIZE);
    sRecordInit = true;
    sRecordInitStarted = false;
    display_setNotice("", "", "", 0);

    printf("REC init\n");
}

//------------------------------------------------------------------------------
bool record_ready()
{
    return sRecordInit;
}

//------------------------------------------------------------------------------
void record_start()
{
    sRecordActive = true;
    sRamBufPos = REC_HEADER_SIZE;
    sFlashPos = 0;

    // write the header information into the first buffer
    REC_HEADER_t header;
    header.magic = REC_MAGIC;
    header.size = REC_FLASH_SIZE;
    memcpy(sDataBuffer, &header, REC_HEADER_SIZE);

    printf("REC start\n");
}

//------------------------------------------------------------------------------
uint32_t record_percentage()
{
    uint32_t p = sRecordActive ? ((sFlashPos * 100) / REC_FLASH_SIZE): 0;
    return p;
}

//------------------------------------------------------------------------------
uint32_t record_replay_size()
{
    const REC_HEADER_t *pkRecHead = (const REC_HEADER_t *)pkFlashRec;
    return (pkRecHead->magic == REC_MAGIC) ? pkRecHead->size : 0;
}

//------------------------------------------------------------------------------
uint32_t replay_percentage()
{
    uint32_t p = ((100 * sReplayPos) / record_replay_size());
    return p;
}

//------------------------------------------------------------------------------
void record_stop()
{
    sRecordActive = false;
    printf("REC stop %lX\n", *((const uint32_t*)pkFlashRec));
}

//------------------------------------------------------------------------------
uint32_t record_replay()
{
    // return the current data record
    uint32_t rec = *((const uint32_t*)(pkFlashRec + REC_HEADER_SIZE + sReplayPos));

    // advance to next record
    sReplayPos += sizeof(uint32_t);
    if (sReplayPos >= record_replay_size())
    {
        // rewind
        sReplayPos = 0;
    }

    return rec;
}

//------------------------------------------------------------------------------
bool record_active()
{
    return sRecordActive;
}

//------------------------------------------------------------------------------
bool record_isrecdata(const uint8_t *pkData)
{
    return ((pkData >= (const uint8_t*)&sDataBuffer[0]) &&
            (pkData <= (const uint8_t*)&sDataBuffer[REC_RAMBUF_SIZE*2-1]));
}

//------------------------------------------------------------------------------
bool record_add(uint32_t data)
{
    bool added = false;

    // check whether recording is active
    if (sRecordActive)
    {
        // check if storage has been initialized
        if (sRecordInit)
        {
            if ((sFlashPos == 0) && (sRamBufPos < 4))
            {
                printf("REC ADD %lu %lX\n", sRamBufPos, data);
            }

            // add the new data record to the RAM buffer
            sDataBuffer[sRamBufPos++] = data;
            added = true;

            // when the RAM buffer is half full, write the data to flash
            // this is done on CPU1 in order not to interfere with data
            // input
            if (sRamBufPos == REC_RAMBUF_SIZE)
            {
                static bool sPrint1 = false;
                if (!sPrint1)
                {
                    printf("REC PUSH 1 %lu %lX\n", sRamBufPos, sDataBuffer[0]);
                    sPrint1 = true;
                }
                
                if (!multicore_fifo_push_timeout_us((uint32_t)&sDataBuffer[0], 0))
                {
                    printf("!");
                }
            }
            if (sRamBufPos == (2*REC_RAMBUF_SIZE))
            {
                static bool sPrint2 = false;
                if (!sPrint2)
                {
                    printf("REC PUSH 2 %lu %lX\n", sRamBufPos, sDataBuffer[REC_RAMBUF_SIZE]);
                    sPrint2 = true;
                }

                // circular buffer, start again at beginning
                sRamBufPos = 0;

                if (!multicore_fifo_push_timeout_us((uint32_t)&sDataBuffer[REC_RAMBUF_SIZE], 0))
                {
                    printf("!");
                }
            }
        }
    }

    return added;
}

//------------------------------------------------------------------------------
bool record_write_flash(const uint8_t *pkData, uint32_t size)
{
    bool full = false;

    static uint32_t sWriteCounter = 0;

    // write to flash
    if (sRecordInit && (sFlashPos < (REC_FLASH_SIZE-size)))
    {
        if (sFlashPos == 0)
        {
            printf("REC FL %lX %lX %lu ", *((const uint32_t*)pkData),
                *((const uint32_t*)pkFlashRec), size);
        }

        flash_range_program(REC_FLASH_OFFSET+sFlashPos, pkData, size);

        if (sFlashPos == 0)
        {
            printf("PRG %lX\n", *((const uint32_t*)pkFlashRec));
        }

        sFlashPos += size;
    }
    else if (!sRecordInit)
    {
        // initialize the flash region first
        record_init();
    }

    if (sFlashPos >= (REC_FLASH_SIZE-size))
    {
        // recording full, stop
        full = true;
        record_stop();
    }

    return full;
}

//------------------------------------------------------------------------------
const uint8_t *record_data()
{
    return pkFlashRec;
}
